polpo/open-retro-storage-frontpanel/sw-frontpanel/main/web_server.cpp

// SPDX-License-Identifier: GPL-2.0-only
//
//  Copyright (C) 2025  Ian Scott
//
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
#include "web_server.h"
#include <string.h>
#include <stdlib.h>
#include <ctype.h>
#include <inttypes.h>
#include <sys/param.h>  // MIN()
#include "esp_log.h"
#include "esp_http_server.h"
#include "esp_system.h"
#include "esp_app_desc.h"
#include "cJSON.h"
#include "interface_common.h"
#include "json_stream.h"
#include "ota_manager.h"
#include "wifi_manager.h"
#ifdef CONFIG_PANEL_TEST_HOOKS
#include <strings.h>
#include "freertos/FreeRTOS.h"
#include "freertos/task.h"
#include "gpio_handler.h"
#include "test_hooks.h"
#endif

static const char *TAG = "web_server";

// Forward declarations
static esp_err_t static_file_handler(httpd_req_t *req);
static esp_err_t api_status_handler(httpd_req_t *req);
static esp_err_t api_images_handler(httpd_req_t *req);
static esp_err_t api_select_entry_handler(httpd_req_t *req);
static esp_err_t api_eject_image_handler(httpd_req_t *req);
static esp_err_t api_prev_image_handler(httpd_req_t *req);
static esp_err_t api_next_image_handler(httpd_req_t *req);
static esp_err_t api_wifi_scan_handler(httpd_req_t *req);
static esp_err_t api_wifi_connect_handler(httpd_req_t *req);
static esp_err_t api_wifi_status_handler(httpd_req_t *req);
static esp_err_t api_settings_get_handler(httpd_req_t *req);
static esp_err_t api_settings_set_handler(httpd_req_t *req);
static esp_err_t api_firmware_check_handler(httpd_req_t *req);
static esp_err_t api_firmware_update_handler(httpd_req_t *req);
static esp_err_t api_firmware_status_handler(httpd_req_t *req);
#ifdef CONFIG_PRODUCT_BLUESCSI
static esp_err_t api_initiator_handler(httpd_req_t *req);
static esp_err_t api_mainboard_firmware_check_handler(httpd_req_t *req);
static esp_err_t api_mainboard_firmware_update_handler(httpd_req_t *req);
static esp_err_t api_mainboard_firmware_status_handler(httpd_req_t *req);
static esp_err_t api_mainboard_firmware_upload_handler(httpd_req_t *req);
static esp_err_t api_panel_firmware_upload_handler(httpd_req_t *req);
static esp_err_t api_delete_handler(httpd_req_t *req);
static esp_err_t api_rename_handler(httpd_req_t *req);
static esp_err_t api_touch_handler(httpd_req_t *req);
static esp_err_t api_mkdir_handler(httpd_req_t *req);
#endif
static esp_err_t api_devices_handler(httpd_req_t *req);
static esp_err_t api_upload_handler(httpd_req_t *req);
static esp_err_t api_download_handler(httpd_req_t *req);
#ifdef CONFIG_PANEL_TEST_HOOKS
static esp_err_t api_button_handler(httpd_req_t *req);
static esp_err_t api_ui_handler(httpd_req_t *req);
static esp_err_t api_screen_handler(httpd_req_t *req);
#endif

// Global server instance for handlers
static web_server_t *g_server = NULL;

// Helper: extract device index from the JSON body. Every request that operates on
// a device should include it in the body, so if there is not one, return false.
static bool get_device_from_body(httpd_req_t *req, uint16_t *device_index) {
    if (req->content_len == 0 || req->content_len > 256) return false;
    char buf[256];
    int len = httpd_req_recv(req, buf, sizeof(buf) - 1);
    if (len <= 0) return false;
    buf[len] = '\0';
    cJSON *json = cJSON_Parse(buf);
    if (!json) return false;
    cJSON *dev = cJSON_GetObjectItem(json, "device");
    bool found = cJSON_IsNumber(dev);
    if (found) *device_index = (uint16_t)dev->valueint;
    cJSON_Delete(json);
    return found;
}

#ifdef CONFIG_PANEL_TEST_HOOKS
// Button ids as wired in main.c: 0=UP 1=SELECT 2=DOWN 3=BACK.
static int button_id_from_name(const char *name) {
    if (!name) return -1;
    if (!strcasecmp(name, "up"))     return 0;
    if (!strcasecmp(name, "select")) return 1;
    if (!strcasecmp(name, "down"))   return 2;
    if (!strcasecmp(name, "back"))   return 3;
    return -1;
}

// POST /api/button  {"button":"down","type":"click","count":1}
// Only click and repeat exist as far as the UI is concerned; the other event
// types the driver emits are never matched by handle_button_event().
static esp_err_t api_button_handler(httpd_req_t *req) {
    char buf[192];
    if (req->content_len == 0 || req->content_len >= sizeof(buf)) {
        httpd_resp_send_err(req, HTTPD_400_BAD_REQUEST, "body required");
        return ESP_FAIL;
    }
    int len = httpd_req_recv(req, buf, sizeof(buf) - 1);
    if (len <= 0) {
        httpd_resp_send_err(req, HTTPD_400_BAD_REQUEST, "short read");
        return ESP_FAIL;
    }
    buf[len] = '\0';

    cJSON *json = cJSON_Parse(buf);
    if (!json) {
        httpd_resp_send_err(req, HTTPD_400_BAD_REQUEST, "bad json");
        return ESP_FAIL;
    }

    cJSON *jb = cJSON_GetObjectItem(json, "button");
    int id = cJSON_IsString(jb) ? button_id_from_name(jb->valuestring)
           : (cJSON_IsNumber(jb) ? jb->valueint : -1);

    cJSON *jt = cJSON_GetObjectItem(json, "type");
    button_event_type_t type = BUTTON_EVENT_CLICK;
    if (cJSON_IsString(jt) && !strcasecmp(jt->valuestring, "repeat")) {
        type = BUTTON_EVENT_REPEAT;
    }

    cJSON *jc = cJSON_GetObjectItem(json, "count");
    int count = cJSON_IsNumber(jc) ? jc->valueint : 1;
    cJSON_Delete(json);

    if (id < 0 || id > 3) {
        httpd_resp_send_err(req, HTTPD_400_BAD_REQUEST, "button must be up|select|down|back");
        return ESP_FAIL;
    }
    if (count < 1 || count > 32) {
        httpd_resp_send_err(req, HTTPD_400_BAD_REQUEST, "count must be 1..32");
        return ESP_FAIL;
    }

    int sent = 0;
    esp_err_t err = ESP_OK;
    for (int i = 0; i < count; i++) {
        err = gpio_handler_inject_event((uint8_t)id, type);
        if (err != ESP_OK) break;
        sent++;
        // Let gpio_event_task drain and the UI settle between presses, so a
        // burst behaves like a person pressing rather than a queue dump.
        vTaskDelay(pdMS_TO_TICKS(30));
    }

    httpd_resp_set_type(req, "application/json");
    JsonStreamWriter jw(req);
    jw.beginObject();
    jw.write("success", err == ESP_OK);
    jw.write("sent", (int)sent);
    if (err != ESP_OK) jw.write("error", esp_err_to_name(err));
    jw.endObject();
    return jw.finalize();
}

// GET /api/ui - what the panel is showing right now.
static esp_err_t api_ui_handler(httpd_req_t *req) {
    panel_ui_state_t st;
    panel_get_ui_state(&st);

    httpd_resp_set_type(req, "application/json");
    JsonStreamWriter jw(req);
    jw.beginObject();
    jw.write("screen", st.screen_name);
    jw.write("screen_id", (int)st.screen);
    jw.write("has_menu", st.has_menu);
    jw.write("cursor", (uint32_t)st.cursor);
    jw.write("count", (uint32_t)st.count);
    jw.write("entry_index", (int)st.entry_index);
    jw.write("selected", st.selected);
    jw.write("display_state", st.display_state_name ? st.display_state_name : "UNKNOWN");
    jw.endObject();
    return jw.finalize();
}

// GET /api/screen - raw u8g2 tile buffer. Geometry rides in headers so the host
// converter does not hardcode the panel or its rotation.
static esp_err_t api_screen_handler(httpd_req_t *req) {
    int tw = 0, th = 0, rot = -1;
    uint8_t *buf = (uint8_t *)malloc(PANEL_FB_MAX_BYTES);
    if (!buf) {
        httpd_resp_send_err(req, HTTPD_500_INTERNAL_SERVER_ERROR, "oom");
        return ESP_FAIL;
    }
    size_t len = panel_get_framebuffer(buf, PANEL_FB_MAX_BYTES, &tw, &th, &rot);
    if (len == 0) {
        free(buf);
        httpd_resp_send_err(req, HTTPD_500_INTERNAL_SERVER_ERROR, "no framebuffer");
        return ESP_FAIL;
    }
    char v[16];
    snprintf(v, sizeof(v), "%d", tw);  httpd_resp_set_hdr(req, "X-Panel-Tile-Width", v);
    char v2[16];
    snprintf(v2, sizeof(v2), "%d", th); httpd_resp_set_hdr(req, "X-Panel-Tile-Height", v2);
    char v3[16];
    snprintf(v3, sizeof(v3), "%d", rot); httpd_resp_set_hdr(req, "X-Panel-Rotation", v3);
    httpd_resp_set_type(req, "application/octet-stream");
    esp_err_t ret = httpd_resp_send(req, (const char *)buf, len);
    free(buf);
    return ret;
}
#endif // CONFIG_PANEL_TEST_HOOKS

// Global OTA manager instance
static ota_manager_t g_ota_manager;

#ifdef CONFIG_PRODUCT_BLUESCSI
static TaskHandle_t g_ota_task_handle = NULL;

// Background OTA task - processes OTA update without blocking HTTP handler
static void web_firmware_update_task(void *pvParameters) {
    ota_manager_t *ota = (ota_manager_t *)pvParameters;

    while (1) {
        esp_err_t ret = ota_manager_process(ota);
        if (ret != ESP_OK && ret != ESP_ERR_NOT_FINISHED) {
            ESP_LOGE(TAG, "OTA process error: %s", esp_err_to_name(ret));
            break;
        }

        ota_state_t state = ota_manager_get_state(ota);

        if (state == OTA_STATE_SUCCESS) {
            ESP_LOGI(TAG, "Web OTA update successful, restarting in 3 seconds...");
            vTaskDelay(pdMS_TO_TICKS(3000));
            esp_restart();
        } else if (state == OTA_STATE_ERROR) {
            ESP_LOGE(TAG, "Web OTA update failed");
            break;
        }

        taskYIELD();
    }

    g_ota_task_handle = NULL;
    vTaskDelete(NULL);
}
#endif

// Embedded file content (gzipped, symbols created by CMakeLists.txt)
extern const uint8_t index_html_gz_start[] asm("_binary_index_html_gz_start");
extern const uint8_t index_html_gz_end[] asm("_binary_index_html_gz_end");
extern const uint8_t app_js_gz_start[] asm("_binary_app_js_gz_start");
extern const uint8_t app_js_gz_end[] asm("_binary_app_js_gz_end");
extern const uint8_t sha256_js_gz_start[] asm("_binary_sha256_js_gz_start");
extern const uint8_t sha256_js_gz_end[] asm("_binary_sha256_js_gz_end");
extern const uint8_t logo_svg_gz_start[] asm("_binary_logo_svg_gz_start");
extern const uint8_t logo_svg_gz_end[] asm("_binary_logo_svg_gz_end");

// Static file descriptor for common handler
typedef struct {
    const uint8_t *start;
    const uint8_t *end;
    const char *content_type;
} static_file_t;

static const static_file_t file_index_html = {
    index_html_gz_start, index_html_gz_end, "text/html; charset=utf-8"
};
static const static_file_t file_app_js = {
    app_js_gz_start, app_js_gz_end, "application/javascript; charset=utf-8"
};
static const static_file_t file_sha256_js = {
    sha256_js_gz_start, sha256_js_gz_end, "application/javascript; charset=utf-8"
};
static const static_file_t file_logo_svg = {
    logo_svg_gz_start, logo_svg_gz_end, "image/svg+xml"
};

// URI handlers
static const httpd_uri_t uri_handlers[] = {
    { .uri = "/", .method = HTTP_GET, .handler = static_file_handler, .user_ctx = (void *)&file_index_html },
    { .uri = "/app.js", .method = HTTP_GET, .handler = static_file_handler, .user_ctx = (void *)&file_app_js },
    { .uri = "/sha256.js", .method = HTTP_GET, .handler = static_file_handler, .user_ctx = (void *)&file_sha256_js },
    { .uri = "/logo.svg", .method = HTTP_GET, .handler = static_file_handler, .user_ctx = (void *)&file_logo_svg },
    { .uri = "/api/status", .method = HTTP_GET, .handler = api_status_handler, .user_ctx = NULL },
    { .uri = "/api/devices", .method = HTTP_GET, .handler = api_devices_handler, .user_ctx = NULL },
    { .uri = "/api/images", .method = HTTP_GET, .handler = api_images_handler, .user_ctx = NULL },
    { .uri = "/api/select_entry", .method = HTTP_POST, .handler = api_select_entry_handler, .user_ctx = NULL },
    { .uri = "/api/eject_image", .method = HTTP_POST, .handler = api_eject_image_handler, .user_ctx = NULL },
    { .uri = "/api/prev_image", .method = HTTP_POST, .handler = api_prev_image_handler, .user_ctx = NULL },
    { .uri = "/api/next_image", .method = HTTP_POST, .handler = api_next_image_handler, .user_ctx = NULL },
    { .uri = "/api/wifi/scan", .method = HTTP_GET, .handler = api_wifi_scan_handler, .user_ctx = NULL },
    { .uri = "/api/wifi/connect", .method = HTTP_POST, .handler = api_wifi_connect_handler, .user_ctx = NULL },
    { .uri = "/api/wifi/status", .method = HTTP_GET, .handler = api_wifi_status_handler, .user_ctx = NULL },
    { .uri = "/api/settings", .method = HTTP_GET, .handler = api_settings_get_handler, .user_ctx = NULL },
    { .uri = "/api/settings", .method = HTTP_POST, .handler = api_settings_set_handler, .user_ctx = NULL },
    { .uri = "/api/firmware/check", .method = HTTP_GET, .handler = api_firmware_check_handler, .user_ctx = NULL },
    { .uri = "/api/firmware/update", .method = HTTP_POST, .handler = api_firmware_update_handler, .user_ctx = NULL },
    { .uri = "/api/firmware/status", .method = HTTP_GET, .handler = api_firmware_status_handler, .user_ctx = NULL },
#ifdef CONFIG_PRODUCT_BLUESCSI
    { .uri = "/api/initiator", .method = HTTP_GET, .handler = api_initiator_handler, .user_ctx = NULL },
    { .uri = "/api/firmware/mainboard/check", .method = HTTP_GET, .handler = api_mainboard_firmware_check_handler, .user_ctx = NULL },
    { .uri = "/api/firmware/mainboard/update", .method = HTTP_POST, .handler = api_mainboard_firmware_update_handler, .user_ctx = NULL },
    { .uri = "/api/firmware/mainboard/status", .method = HTTP_GET, .handler = api_mainboard_firmware_status_handler, .user_ctx = NULL },
    { .uri = "/api/firmware/mainboard/upload", .method = HTTP_POST, .handler = api_mainboard_firmware_upload_handler, .user_ctx = NULL },
    { .uri = "/api/firmware/panel/upload", .method = HTTP_POST, .handler = api_panel_firmware_upload_handler, .user_ctx = NULL },
    { .uri = "/api/delete", .method = HTTP_POST, .handler = api_delete_handler, .user_ctx = NULL },
    { .uri = "/api/rename", .method = HTTP_POST, .handler = api_rename_handler, .user_ctx = NULL },
    { .uri = "/api/touch", .method = HTTP_POST, .handler = api_touch_handler, .user_ctx = NULL },
    { .uri = "/api/mkdir", .method = HTTP_POST, .handler = api_mkdir_handler, .user_ctx = NULL },
#endif
    { .uri = "/api/upload", .method = HTTP_POST, .handler = api_upload_handler, .user_ctx = NULL },
    { .uri = "/api/download", .method = HTTP_GET, .handler = api_download_handler, .user_ctx = NULL },
#ifdef CONFIG_PANEL_TEST_HOOKS
    { .uri = "/api/button", .method = HTTP_POST, .handler = api_button_handler, .user_ctx = NULL },
    { .uri = "/api/ui", .method = HTTP_GET, .handler = api_ui_handler, .user_ctx = NULL },
    { .uri = "/api/screen", .method = HTTP_GET, .handler = api_screen_handler, .user_ctx = NULL }
#endif
};

// ETag for the embedded web assets, based on the build's ELF hash
static char s_asset_etag[CONFIG_APP_RETRIEVE_LEN_ELF_SHA + 3];

static void asset_etag_init(void) {
    char sha[CONFIG_APP_RETRIEVE_LEN_ELF_SHA + 1] = {0};
    esp_app_get_elf_sha256(sha, sizeof(sha));
    // ETags must be double-quoted per RFC 9110
    snprintf(s_asset_etag, sizeof(s_asset_etag), "\"%s\"", sha);
}

static esp_err_t static_file_handler(httpd_req_t *req) {
    const static_file_t *file = (const static_file_t *)req->user_ctx;

    httpd_resp_set_type(req, file->content_type);
    httpd_resp_set_hdr(req, "Cache-Control", "no-cache");
    httpd_resp_set_hdr(req, "ETag", s_asset_etag);

    char if_none_match[sizeof(s_asset_etag)];
    if (httpd_req_get_hdr_value_str(req, "If-None-Match", if_none_match, sizeof(if_none_match)) == ESP_OK &&
        strcmp(if_none_match, s_asset_etag) == 0) {
        httpd_resp_set_status(req, "304 Not Modified");
        return httpd_resp_send(req, NULL, 0);
    }

    httpd_resp_set_hdr(req, "Content-Encoding", "gzip");
    return httpd_resp_send(req, (const char *)file->start, file->end - file->start);
}

static esp_err_t api_status_handler(httpd_req_t *req) {
    httpd_resp_set_type(req, "application/json");

    JsonStreamWriter json(req);
    esp_err_t ret = json.beginObject();
    if (ret != ESP_OK) return ret;

    if (g_server && g_server->interface_ctx) {
        system_info_t sys_info;
        esp_err_t info_ret = interface_get_system_info(g_server->interface_ctx, &sys_info);
        if (info_ret == ESP_OK) {
            ret = json.write("main_firmware", sys_info.main_firmware_version);
            if (ret != ESP_OK) return ret;
            ret = json.write("panel_firmware", sys_info.panel_firmware_version);
            if (ret != ESP_OK) return ret;
            ret = json.write("transport", sys_info.transport_name);
            if (ret != ESP_OK) return ret;
            ret = json.write("host_connected", sys_info.host_connected ? 1 : 0);
            if (ret != ESP_OK) return ret;
            ret = json.write("free_memory", sys_info.free_memory);
            if (ret != ESP_OK) return ret;
            ret = json.write("uptime", sys_info.uptime_seconds);
            if (ret != ESP_OK) return ret;
        } else {
            ret = json.write("main_firmware", "");
            if (ret != ESP_OK) return ret;
            ret = json.write("panel_firmware", "");
            if (ret != ESP_OK) return ret;
            ret = json.write("transport", "None");
            if (ret != ESP_OK) return ret;
            ret = json.write("host_connected", 0);
            if (ret != ESP_OK) return ret;
            ret = json.write("free_memory", (uint32_t)esp_get_free_heap_size());
            if (ret != ESP_OK) return ret;
            ret = json.write("uptime", (uint32_t)(esp_log_timestamp() / 1000));
            if (ret != ESP_OK) return ret;
        }
    } else {
        ret = json.write("main_firmware", "");
        if (ret != ESP_OK) return ret;
        ret = json.write("panel_firmware", "");
        if (ret != ESP_OK) return ret;
        ret = json.write("transport", "None");
        if (ret != ESP_OK) return ret;
        ret = json.write("host_connected", 0);
        if (ret != ESP_OK) return ret;
        ret = json.write("free_memory", (uint32_t)esp_get_free_heap_size());
        if (ret != ESP_OK) return ret;
        ret = json.write("uptime", (uint32_t)(esp_log_timestamp() / 1000));
        if (ret != ESP_OK) return ret;
    }

    ret = json.write("product_name", PRODUCT_NAME_SHORT);
    if (ret != ESP_OK) return ret;
    ret = json.write("product_full", PRODUCT_NAME_FULL);
    if (ret != ESP_OK) return ret;
    ret = json.write("hostname", (g_server && g_server->interface_ctx)
                                     ? wifi_manager_get_mdns_hostname(g_server->interface_ctx->wifi_manager)
                                     : WIFI_MANAGER_MDNS_HOSTNAME_DEFAULT);
    if (ret != ESP_OK) return ret;
    ret = json.write("logo_url", PRODUCT_LOGO_URL);
    if (ret != ESP_OK) return ret;

    ret = json.endObject();
    if (ret != ESP_OK) return ret;

    return json.finalize();
}

#ifdef CONFIG_PRODUCT_BLUESCSI
static const char *initiator_phase_name(uint8_t phase) {
    switch (phase) {
        case PANEL_INITIATOR_PHASE_SCANNING: return "scanning";
        case PANEL_INITIATOR_PHASE_IMAGING:  return "imaging";
        case PANEL_INITIATOR_PHASE_COMPLETE: return "complete";
        case PANEL_INITIATOR_PHASE_ERROR:    return "error";
        default:                             return "idle";
    }
}

/* Serves the status the display task already polls. Issuing our own transaction
 * here would put a browser refresh in contention with the display task for the
 * host_comm mutex, against a main board that may be mid-spin-up. */
static esp_err_t api_initiator_handler(httpd_req_t *req) {
    httpd_resp_set_type(req, "application/json");

    JsonStreamWriter json(req);
    esp_err_t ret = json.beginObject();
    if (ret != ESP_OK) return ret;

    int target_count = 0;
    const initiator_status_response_t *st = panel_get_initiator_status(&target_count);

    ret = json.write("mode", panel_in_initiator_mode() ? 1 : 0);
    if (ret != ESP_OK) return ret;

    if (!st || !panel_in_initiator_mode()) {
        ret = json.endObject();
        if (ret != ESP_OK) return ret;
        return json.finalize();
    }

    // Progress comes from the synchronous summary, which is current even while
    // the board is imaging. The per-target list below comes from the async
    // status and may be older.
    const panel_initiator_summary_t *sum = panel_get_initiator_summary();

    ret = json.write("phase", (int)sum->phase);
    if (ret != ESP_OK) return ret;
    ret = json.write("phase_name", initiator_phase_name(sum->phase));
    if (ret != ESP_OK) return ret;
    ret = json.write("progress", (int)sum->progress);
    if (ret != ESP_OK) return ret;
    ret = json.write("initiator_id", (int)st->initiator_id);
    if (ret != ESP_OK) return ret;
    ret = json.write("current_target", (int)sum->current_target);
    if (ret != ESP_OK) return ret;
    ret = json.write("targets_found", (int)sum->targets_found);
    if (ret != ESP_OK) return ret;
    ret = json.write("targets_imaged", (int)sum->targets_imaged);
    if (ret != ESP_OK) return ret;
    // Identity of the target in progress, so the page can say what it is
    // working on rather than just how fast. From the summary, because the
    // per-target table below does not arrive while the board is imaging.
    ret = json.write("device_type", (int)sum->device_type);
    if (ret != ESP_OK) return ret;
    ret = json.write("vendor", sum->vendor);
    if (ret != ESP_OK) return ret;
    ret = json.write("product", sum->product);
    if (ret != ESP_OK) return ret;
    ret = json.write("size_kb",
                     (uint32_t)((uint64_t)sum->sectorcount * sum->sectorsize / 1024));
    if (ret != ESP_OK) return ret;
    ret = json.write("speed_kbps", (uint32_t)sum->speed_kbps);
    if (ret != ESP_OK) return ret;
    ret = json.write("filename", st->current_filename);
    if (ret != ESP_OK) return ret;

    ret = json.writeKey("targets");
    if (ret != ESP_OK) return ret;
    ret = json.beginArray();
    if (ret != ESP_OK) return ret;

    for (int i = 0; i < target_count; i++) {
        const initiator_target_info_t *t = &st->targets[i];
        char vendor[9], product[17];
        memcpy(vendor, t->vendor, 8);   vendor[8] = '\0';
        memcpy(product, t->product, 16); product[16] = '\0';
        for (int j = 7; j >= 0 && vendor[j] == ' '; j--) vendor[j] = '\0';
        for (int j = 15; j >= 0 && product[j] == ' '; j--) product[j] = '\0';

        ret = json.beginObject();
        if (ret != ESP_OK) return ret;
        ret = json.write("id", (int)t->scsi_id);
        if (ret != ESP_OK) return ret;
        ret = json.write("type", (int)t->device_type);
        if (ret != ESP_OK) return ret;
        ret = json.write("status", (int)t->status);
        if (ret != ESP_OK) return ret;
        ret = json.write("skip_reason", (int)t->skip_reason);
        if (ret != ESP_OK) return ret;
        ret = json.write("vendor", vendor);
        if (ret != ESP_OK) return ret;
        ret = json.write("product", product);
        if (ret != ESP_OK) return ret;
        ret = json.write("sectors", t->sectorcount);
        if (ret != ESP_OK) return ret;
        ret = json.write("sector_size", t->sectorsize);
        if (ret != ESP_OK) return ret;
        ret = json.write("sectors_done", t->sectors_done);
        if (ret != ESP_OK) return ret;
        ret = json.write("bad_sectors", t->bad_sector_count);
        if (ret != ESP_OK) return ret;
        ret = json.endObject();
        if (ret != ESP_OK) return ret;
    }

    ret = json.endArray();
    if (ret != ESP_OK) return ret;
    ret = json.endObject();
    if (ret != ESP_OK) return ret;
    return json.finalize();
}
#endif // CONFIG_PRODUCT_BLUESCSI

static esp_err_t api_devices_handler(httpd_req_t *req) {
    httpd_resp_set_type(req, "application/json");

    JsonStreamWriter json(req);
    esp_err_t ret = json.beginObject();
    if (ret != ESP_OK) return ret;

    if (g_server && g_server->interface_ctx) {
        uint16_t active_device = g_server->interface_ctx->active_device_index;
        ret = json.write("active_device", (int)active_device);
        if (ret != ESP_OK) return ret;

        // Get device list from host
        uint8_t buf[sizeof(device_list_response_t) + CONFIG_MAX_DEVICES * sizeof(device_summary_t)];
        device_list_response_t *list = (device_list_response_t *)buf;

        esp_err_t list_ret = interface_get_device_list(g_server->interface_ctx, list, sizeof(buf));

        if (list_ret == ESP_OK) {
            ret = json.write("device_count", (int)list->device_count);
            if (ret != ESP_OK) return ret;
#ifdef CONFIG_PRODUCT_BLUESCSI
            // In initiator mode there are no emulated devices; the web UI needs
            // to know that rather than reading the empty list as a failure.
            ret = json.write("mode", (int)PANEL_DEVLIST_MODE(list));
            if (ret != ESP_OK) return ret;
#endif

            ret = json.writeKey("devices");
            if (ret != ESP_OK) return ret;
            ret = json.beginArray();
            if (ret != ESP_OK) return ret;

            for (uint8_t i = 0; i < list->device_count; i++) {
                ret = json.beginObject();
                if (ret != ESP_OK) return ret;

                ret = json.write("index", (int)list->devices[i].device_index);
                if (ret != ESP_OK) return ret;
                ret = json.write("type", (int)list->devices[i].device_type);
                if (ret != ESP_OK) return ret;
                ret = json.write("status", (int)list->devices[i].device_status);
                if (ret != ESP_OK) return ret;
                ret = json.write("label", list->devices[i].device_label);
                if (ret != ESP_OK) return ret;
                ret = json.write("image", list->devices[i].image_name);
                if (ret != ESP_OK) return ret;

                ret = json.endObject();
                if (ret != ESP_OK) return ret;
            }

            ret = json.endArray();
            if (ret != ESP_OK) return ret;
        } else {
            ret = json.write("device_count", 0);
            if (ret != ESP_OK) return ret;
            ret = json.writeKey("devices");
            if (ret != ESP_OK) return ret;
            ret = json.beginArray();
            if (ret != ESP_OK) return ret;
            ret = json.endArray();
            if (ret != ESP_OK) return ret;
            ret = json.write("error", esp_err_to_name(list_ret));
            if (ret != ESP_OK) return ret;
        }
    } else {
        ret = json.write("active_device", 0);
        if (ret != ESP_OK) return ret;
        ret = json.write("device_count", 0);
        if (ret != ESP_OK) return ret;
        ret = json.writeKey("devices");
        if (ret != ESP_OK) return ret;
        ret = json.beginArray();
        if (ret != ESP_OK) return ret;
        ret = json.endArray();
        if (ret != ESP_OK) return ret;
    }

    ret = json.endObject();
    if (ret != ESP_OK) return ret;

    return json.finalize();
}

static esp_err_t api_images_handler(httpd_req_t *req) {
    httpd_resp_set_type(req, "application/json");

    // The ?device= query parameter names the device this listing is for.
    // On BlueSCSI: used for the device's loaded image status
    // On PicoIDE: loaded image status, per-device browse dir, extension filter
    //
    // Unlike the commands that act on a device, a listing is a read and can fall
    // back to the panel's own selection — the same value /api/devices reports as
    // active_device. A client that has no device list yet (BlueSCSI reports none
    // while imaging in initiator mode) can still browse the card, and adopts the
    // echoed index for its next request.
    uint16_t device_index = (g_server && g_server->interface_ctx)
        ? g_server->interface_ctx->active_device_index : 0;
    {
        char query[64];
        char device_str[8];
        if (httpd_req_get_url_query_len(req) > 0 &&
            httpd_req_get_url_query_str(req, query, sizeof(query)) == ESP_OK &&
            httpd_query_key_value(query, "device", device_str, sizeof(device_str)) == ESP_OK) {
            device_index = (uint16_t)atoi(device_str);
        }
    }

    JsonStreamWriter json(req);
    esp_err_t ret = json.beginObject();
    if (ret != ESP_OK) return ret;

    if (g_server && g_server->interface_ctx) {
        host_comm_t *host_comm = g_server->interface_ctx->host_comm;

        ret = json.write("device", (int)device_index);
        if (ret != ESP_OK) return ret;

        // Get current path
        char current_path[256] = "/";
        if (host_comm && host_comm->link_up) {
            host_comm_get_current_path(host_comm, device_index, current_path, sizeof(current_path));
        }
        ret = json.write("current_path", current_path);
        if (ret != ESP_OK) return ret;

        // Get loaded image status
        loaded_image_status_t image_status = {};
        bool have_image_status = false;
        if (host_comm && host_comm->link_up) {
            have_image_status = (host_comm_get_loaded_image_status(host_comm, device_index, &image_status) == ESP_OK);
        }

        if (have_image_status && image_status.image_loaded) {
            ret = json.write("current_image", image_status.image_name);
            if (ret != ESP_OK) return ret;
            ret = json.write("image_index", image_status.image_index);
            if (ret != ESP_OK) return ret;
            ret = json.write("total_images", image_status.total_images);
            if (ret != ESP_OK) return ret;
        } else {
            ret = json.write("current_image", (const char*)nullptr);
            if (ret != ESP_OK) return ret;
            ret = json.write("image_index", 0);
            if (ret != ESP_OK) return ret;
            ret = json.write("total_images", 0);
            if (ret != ESP_OK) return ret;
        }

        // Start entries array
        ret = json.writeKey("entries");
        if (ret != ESP_OK) return ret;

        ret = json.beginArray();
        if (ret != ESP_OK) return ret;

        // Stream entries one at a time to avoid stack overflow
        uint32_t entry_count = 0;
        if (host_comm && host_comm->link_up) {
            host_comm_get_entry_count(host_comm, device_index, &entry_count);
        }

        for (uint32_t i = 0; i < entry_count && i < 64; i++) {
            dir_entry_info_t entry;
            if (host_comm_get_entry_info(host_comm, device_index, i, &entry) == ESP_OK) {
                ret = json.beginObject();
                if (ret != ESP_OK) return ret;

                ret = json.write("name", entry.name);
                if (ret != ESP_OK) return ret;

                ret = json.write("is_directory", entry.entry_type == 0);
                if (ret != ESP_OK) return ret;
                // log.txt / bluescsi.ini and friends stay listed so they can be
                // downloaded and edited, but must not offer a Load button.
                ret = json.write("loadable",
                                 (entry.flags & PANEL_ENTRY_FLAG_NOT_LOADABLE) ? 0 : 1);
                if (ret != ESP_OK) return ret;

                ret = json.write("index", (int)i);
                if (ret != ESP_OK) return ret;

                ret = json.endObject();
                if (ret != ESP_OK) return ret;
            }
        }

        ret = json.endArray();
        if (ret != ESP_OK) return ret;
    } else {
        ret = json.write("current_path", "/");
        if (ret != ESP_OK) return ret;

        ret = json.write("current_image", (const char*)nullptr);
        if (ret != ESP_OK) return ret;

        ret = json.write("image_index", 0);
        if (ret != ESP_OK) return ret;

        ret = json.write("total_images", 0);
        if (ret != ESP_OK) return ret;

        ret = json.writeKey("entries");
        if (ret != ESP_OK) return ret;

        ret = json.beginArray();
        if (ret != ESP_OK) return ret;

        ret = json.endArray();
        if (ret != ESP_OK) return ret;
    }

    ret = json.endObject();
    if (ret != ESP_OK) return ret;

    return json.finalize();
}

static esp_err_t api_select_entry_handler(httpd_req_t *req) {
    // Read request body
    char content[100];
    size_t recv_size = MIN(req->content_len, sizeof(content) - 1);
    int ret = httpd_req_recv(req, content, recv_size);
    if (ret <= 0) {
        httpd_resp_send_500(req);
        return ESP_FAIL;
    }
    content[ret] = '\0';

    // Parse JSON
    cJSON *json = cJSON_Parse(content);
    if (!json) {
        httpd_resp_send_err(req, HTTPD_400_BAD_REQUEST, "Invalid JSON");
        return ESP_FAIL;
    }

    cJSON *entry_index_json = cJSON_GetObjectItem(json, "index");
    if (!cJSON_IsNumber(entry_index_json)) {
        cJSON_Delete(json);
        httpd_resp_send_err(req, HTTPD_400_BAD_REQUEST, "Missing or invalid index");
        return ESP_FAIL;
    }

    int32_t entry_index = (int32_t)entry_index_json->valueint;

    // The device to act on is required
    cJSON *device_json = cJSON_GetObjectItem(json, "device");
    if (!cJSON_IsNumber(device_json)) {
        cJSON_Delete(json);
        httpd_resp_send_err(req, HTTPD_400_BAD_REQUEST, "Missing device");
        return ESP_FAIL;
    }
    uint16_t device_index = (uint16_t)device_json->valueint;

    // Send command to host
    httpd_resp_set_type(req, "application/json");

    JsonStreamWriter json_writer(req);
    esp_err_t json_ret = json_writer.beginObject();
    if (json_ret != ESP_OK) {
        cJSON_Delete(json);
        return json_ret;
    }

    bool success = false;
    if (g_server && g_server->interface_ctx) {
        esp_err_t select_ret = interface_select_entry(g_server->interface_ctx, entry_index, device_index);
        success = (select_ret == ESP_OK);
        interface_invalidate_disc_list();
        if (!success) {
            json_ret = json_writer.write("error", esp_err_to_name(select_ret));
            if (json_ret != ESP_OK) {
                cJSON_Delete(json);
                return json_ret;
            }
        }
    } else {
        json_ret = json_writer.write("error", "Interface not available");
        if (json_ret != ESP_OK) {
            cJSON_Delete(json);
            return json_ret;
        }
    }

    json_ret = json_writer.write("success", success);
    if (json_ret != ESP_OK) {
        cJSON_Delete(json);
        return json_ret;
    }

    json_ret = json_writer.endObject();
    if (json_ret != ESP_OK) {
        cJSON_Delete(json);
        return json_ret;
    }

    cJSON_Delete(json);
    return json_writer.finalize();
}

static esp_err_t api_eject_image_handler(httpd_req_t *req) {
    uint16_t device_index;
    if (!get_device_from_body(req, &device_index)) {
        httpd_resp_send_err(req, HTTPD_400_BAD_REQUEST, "Missing device");
        return ESP_FAIL;
    }

    httpd_resp_set_type(req, "application/json");

    JsonStreamWriter json(req);
    esp_err_t ret = json.beginObject();
    if (ret != ESP_OK) return ret;

    bool success = false;
    if (g_server && g_server->interface_ctx) {
        esp_err_t eject_ret = interface_eject_image(g_server->interface_ctx, device_index);
        success = (eject_ret == ESP_OK);
        if (!success) {
            ret = json.write("error", esp_err_to_name(eject_ret));
            if (ret != ESP_OK) return ret;
        }
    } else {
        ret = json.write("error", "Interface not available");
        if (ret != ESP_OK) return ret;
    }

    ret = json.write("success", success);
    if (ret != ESP_OK) return ret;

    ret = json.endObject();
    if (ret != ESP_OK) return ret;

    return json.finalize();
}

static esp_err_t api_prev_image_handler(httpd_req_t *req) {
    uint16_t device_index;
    if (!get_device_from_body(req, &device_index)) {
        httpd_resp_send_err(req, HTTPD_400_BAD_REQUEST, "Missing device");
        return ESP_FAIL;
    }

    httpd_resp_set_type(req, "application/json");

    JsonStreamWriter json(req);
    esp_err_t ret = json.beginObject();
    if (ret != ESP_OK) return ret;

    bool success = false;
    if (g_server && g_server->interface_ctx && g_server->interface_ctx->host_comm) {
        esp_err_t prev_ret = host_comm_select_prev_image(g_server->interface_ctx->host_comm, device_index);
        success = (prev_ret == ESP_OK);
        if (!success) {
            ret = json.write("error", esp_err_to_name(prev_ret));
            if (ret != ESP_OK) return ret;
        }
    } else {
        ret = json.write("error", "Interface not available");
        if (ret != ESP_OK) return ret;
    }

    ret = json.write("success", success);
    if (ret != ESP_OK) return ret;

    ret = json.endObject();
    if (ret != ESP_OK) return ret;

    return json.finalize();
}

static esp_err_t api_next_image_handler(httpd_req_t *req) {
    uint16_t device_index;
    if (!get_device_from_body(req, &device_index)) {
        httpd_resp_send_err(req, HTTPD_400_BAD_REQUEST, "Missing device");
        return ESP_FAIL;
    }

    httpd_resp_set_type(req, "application/json");

    JsonStreamWriter json(req);
    esp_err_t ret = json.beginObject();
    if (ret != ESP_OK) return ret;

    bool success = false;
    if (g_server && g_server->interface_ctx && g_server->interface_ctx->host_comm) {
        esp_err_t next_ret = host_comm_select_next_image(g_server->interface_ctx->host_comm, device_index);
        success = (next_ret == ESP_OK);
        if (!success) {
            ret = json.write("error", esp_err_to_name(next_ret));
            if (ret != ESP_OK) return ret;
        }
    } else {
        ret = json.write("error", "Interface not available");
        if (ret != ESP_OK) return ret;
    }

    ret = json.write("success", success);
    if (ret != ESP_OK) return ret;

    ret = json.endObject();
    if (ret != ESP_OK) return ret;

    return json.finalize();
}

static esp_err_t api_wifi_scan_handler(httpd_req_t *req) {
    httpd_resp_set_type(req, "application/json");

    JsonStreamWriter json(req);
    esp_err_t ret = json.beginObject();
    if (ret != ESP_OK) return ret;

    if (g_server && g_server->interface_ctx && g_server->interface_ctx->wifi_manager) {
        // Start WiFi scan
        esp_err_t scan_ret = wifi_manager_scan_start(g_server->interface_ctx->wifi_manager);

        if (scan_ret != ESP_OK) {
            ret = json.write("error", esp_err_to_name(scan_ret));
            if (ret != ESP_OK) return ret;
        }

        // Get number of APs found
        uint16_t ap_count = 0;
        scan_ret = wifi_manager_scan_get_count(g_server->interface_ctx->wifi_manager, &ap_count);

        if (scan_ret != ESP_OK) {
            ret = json.write("error", esp_err_to_name(scan_ret));
            if (ret != ESP_OK) return ret;
        }

        ret = json.writeKey("networks");
        if (ret != ESP_OK) return ret;

        ret = json.beginArray();
        if (ret != ESP_OK) return ret;

        // Fetch and stream each AP record one at a time
        for (uint16_t i = 0; i < ap_count && i < 32; i++) {
            wifi_ap_info_t ap_info;
            scan_ret = wifi_manager_scan_get_ap(g_server->interface_ctx->wifi_manager, &ap_info);

            if (scan_ret == ESP_OK) {
                ret = json.beginObject();
                if (ret != ESP_OK) {
                    // Clean up remaining APs before returning
                    wifi_manager_scan_cleanup(g_server->interface_ctx->wifi_manager);
                    return ret;
                }

                ret = json.write("ssid", ap_info.ssid);
                if (ret != ESP_OK) {
                    wifi_manager_scan_cleanup(g_server->interface_ctx->wifi_manager);
                    return ret;
                }

                ret = json.write("rssi", ap_info.rssi);
                if (ret != ESP_OK) {
                    wifi_manager_scan_cleanup(g_server->interface_ctx->wifi_manager);
                    return ret;
                }

                ret = json.write("auth_mode", interface_auth_mode_string(ap_info.auth_mode));
                if (ret != ESP_OK) {
                    wifi_manager_scan_cleanup(g_server->interface_ctx->wifi_manager);
                    return ret;
                }

                ret = json.write("has_password", ap_info.has_password ? 1 : 0);
                if (ret != ESP_OK) {
                    wifi_manager_scan_cleanup(g_server->interface_ctx->wifi_manager);
                    return ret;
                }

                ret = json.endObject();
                if (ret != ESP_OK) {
                    wifi_manager_scan_cleanup(g_server->interface_ctx->wifi_manager);
                    return ret;
                }
            }
        }

        // Clean up any remaining AP records (if ap_count > 32)
        wifi_manager_scan_cleanup(g_server->interface_ctx->wifi_manager);

        ret = json.endArray();
        if (ret != ESP_OK) return ret;
    } else {
        // Add mock data when interface is not available
        ret = json.writeKey("networks");
        if (ret != ESP_OK) return ret;

        ret = json.beginArray();
        if (ret != ESP_OK) return ret;

        ret = json.beginObject();
        if (ret != ESP_OK) return ret;

        ret = json.write("ssid", "Example Network");
        if (ret != ESP_OK) return ret;

        ret = json.write("rssi", -45);
        if (ret != ESP_OK) return ret;

        ret = json.write("auth_mode", "WPA2");
        if (ret != ESP_OK) return ret;

        ret = json.write("has_password", 1);
        if (ret != ESP_OK) return ret;

        ret = json.endObject();
        if (ret != ESP_OK) return ret;

        ret = json.endArray();
        if (ret != ESP_OK) return ret;
    }

    ret = json.endObject();
    if (ret != ESP_OK) return ret;

    return json.finalize();
}

static esp_err_t api_wifi_connect_handler(httpd_req_t *req) {
    // Read request body
    char content[256];
    size_t recv_size = MIN(req->content_len, sizeof(content) - 1);
    int ret = httpd_req_recv(req, content, recv_size);
    if (ret <= 0) {
        httpd_resp_send_500(req);
        return ESP_FAIL;
    }
    content[ret] = '\0';

    // Parse JSON
    cJSON *json = cJSON_Parse(content);
    if (!json) {
        httpd_resp_send_err(req, HTTPD_400_BAD_REQUEST, "Invalid JSON");
        return ESP_FAIL;
    }

    cJSON *ssid_json = cJSON_GetObjectItem(json, "ssid");
    cJSON *password_json = cJSON_GetObjectItem(json, "password");

    if (!cJSON_IsString(ssid_json)) {
        cJSON_Delete(json);
        httpd_resp_send_err(req, HTTPD_400_BAD_REQUEST, "Missing or invalid SSID");
        return ESP_FAIL;
    }

    const char *ssid = ssid_json->valuestring;
    const char *password = (cJSON_IsString(password_json)) ? password_json->valuestring : NULL;

    // Connect to WiFi
    httpd_resp_set_type(req, "application/json");

    JsonStreamWriter json_writer(req);
    esp_err_t json_ret = json_writer.beginObject();
    if (json_ret != ESP_OK) {
        cJSON_Delete(json);
        return json_ret;
    }

    bool success = false;
    if (g_server && g_server->interface_ctx) {
        esp_err_t connect_ret = interface_wifi_connect(g_server->interface_ctx, ssid, password);
        success = (connect_ret == ESP_OK);
        if (!success) {
            json_ret = json_writer.write("error", esp_err_to_name(connect_ret));
            if (json_ret != ESP_OK) {
                cJSON_Delete(json);
                return json_ret;
            }
        }
    } else {
        json_ret = json_writer.write("error", "Interface not available");
        if (json_ret != ESP_OK) {
            cJSON_Delete(json);
            return json_ret;
        }
    }

    json_ret = json_writer.write("success", success);
    if (json_ret != ESP_OK) {
        cJSON_Delete(json);
        return json_ret;
    }

    json_ret = json_writer.endObject();
    if (json_ret != ESP_OK) {
        cJSON_Delete(json);
        return json_ret;
    }

    cJSON_Delete(json);
    return json_writer.finalize();
}

static esp_err_t api_wifi_status_handler(httpd_req_t *req) {
    httpd_resp_set_type(req, "application/json");

    JsonStreamWriter json(req);
    esp_err_t ret = json.beginObject();
    if (ret != ESP_OK) return ret;

    if (g_server && g_server->interface_ctx && g_server->interface_ctx->wifi_manager) {
        wifi_manager_t *wifi = g_server->interface_ctx->wifi_manager;
        wifi_manager_state_t state = wifi_manager_get_state(wifi);

        ret = json.write("state", interface_wifi_state_string(state));
        if (ret != ESP_OK) return ret;

        // Determine mode: AP, Client, or None
        const char *mode = "None";
        if (wifi->ap_active) {
            mode = "AP";
        } else if (wifi->station_connected) {
            mode = "Client";
        }
        ret = json.write("mode", mode);
        if (ret != ESP_OK) return ret;

        // Include SSID based on mode
        if (wifi->station_connected) {
            ret = json.write("ssid", wifi->ssid);
            if (ret != ESP_OK) return ret;

            esp_ip4_addr_t ip;
            if (wifi_manager_get_ip_info(wifi, &ip, NULL, NULL) == ESP_OK) {
                char ip_address[16];
                snprintf(ip_address, sizeof(ip_address), IPSTR, IP2STR(&ip));
                ret = json.write("ip_address", ip_address);
                if (ret != ESP_OK) return ret;
            } else {
                ret = json.write("ip_address", "");
                if (ret != ESP_OK) return ret;
            }
        } else if (wifi->ap_active) {
            ret = json.write("ssid", wifi_manager_get_ap_ssid(wifi));
            if (ret != ESP_OK) return ret;

            char ip_address[16];
            snprintf(ip_address, sizeof(ip_address), IPSTR, IP2STR(&wifi->ap_ip_addr));
            ret = json.write("ip_address", ip_address);
            if (ret != ESP_OK) return ret;
        } else {
            ret = json.write("ssid", "");
            if (ret != ESP_OK) return ret;

            ret = json.write("ip_address", "");
            if (ret != ESP_OK) return ret;
        }
    } else {
        ret = json.write("state", "Unavailable");
        if (ret != ESP_OK) return ret;

        ret = json.write("mode", "None");
        if (ret != ESP_OK) return ret;

        ret = json.write("ssid", "");
        if (ret != ESP_OK) return ret;

        ret = json.write("ip_address", "");
        if (ret != ESP_OK) return ret;
    }

    ret = json.endObject();
    if (ret != ESP_OK) return ret;

    return json.finalize();
}

// Panel identity: AP SSID and mDNS hostname
// Defaults are reported so the UI can show them as placeholders
static esp_err_t api_settings_get_handler(httpd_req_t *req) {
    httpd_resp_set_type(req, "application/json");

    JsonStreamWriter json(req);
    esp_err_t ret = json.beginObject();
    if (ret != ESP_OK) return ret;

    char default_ap_ssid[WIFI_MANAGER_SSID_MAX_LEN];
    char default_hostname[WIFI_MANAGER_HOSTNAME_MAX_LEN];
    wifi_manager_default_ap_ssid(default_ap_ssid, sizeof(default_ap_ssid));
    wifi_manager_default_mdns_hostname(default_hostname, sizeof(default_hostname));

    wifi_manager_t *wifi = (g_server && g_server->interface_ctx) ? g_server->interface_ctx->wifi_manager : NULL;

    ret = json.write("ap_ssid", wifi ? wifi_manager_get_ap_ssid(wifi) : default_ap_ssid);
    if (ret != ESP_OK) return ret;
    ret = json.write("mdns_hostname", wifi ? wifi_manager_get_mdns_hostname(wifi) : default_hostname);
    if (ret != ESP_OK) return ret;
    ret = json.write("default_ap_ssid", default_ap_ssid);
    if (ret != ESP_OK) return ret;
    ret = json.write("default_mdns_hostname", default_hostname);
    if (ret != ESP_OK) return ret;

    ret = json.endObject();
    if (ret != ESP_OK) return ret;

    return json.finalize();
}

static esp_err_t api_settings_set_handler(httpd_req_t *req) {
    char content[512];
    size_t recv_size = MIN(req->content_len, sizeof(content) - 1);
    int recv_ret = httpd_req_recv(req, content, recv_size);
    if (recv_ret <= 0) {
        httpd_resp_send_500(req);
        return ESP_FAIL;
    }
    content[recv_ret] = '\0';

    cJSON *json_req = cJSON_Parse(content);
    if (!json_req) {
        httpd_resp_send_err(req, HTTPD_400_BAD_REQUEST, "Invalid JSON");
        return ESP_FAIL;
    }

    wifi_manager_t *wifi = (g_server && g_server->interface_ctx) ? g_server->interface_ctx->wifi_manager : NULL;
    if (!wifi) {
        cJSON_Delete(json_req);
        httpd_resp_send_err(req, HTTPD_500_INTERNAL_SERVER_ERROR, "WiFi manager not available");
        return ESP_FAIL;
    }

    // Any field can be omitted to leave it alone. An empty (but not omitted) field
    // resets it to default
    cJSON *ap_ssid_json = cJSON_GetObjectItem(json_req, "ap_ssid");
    cJSON *ap_password_json = cJSON_GetObjectItem(json_req, "ap_password");
    cJSON *hostname_json = cJSON_GetObjectItem(json_req, "mdns_hostname");
    const char *ap_ssid = cJSON_IsString(ap_ssid_json) ? ap_ssid_json->valuestring : NULL;
    const char *ap_password = cJSON_IsString(ap_password_json) ? ap_password_json->valuestring : NULL;
    const char *hostname = cJSON_IsString(hostname_json) ? hostname_json->valuestring : NULL;

    const char *error = NULL;
    if (ap_ssid && ap_ssid[0] && !wifi_manager_ap_ssid_is_valid(ap_ssid)) {
        error = "Invalid AP name: 1-32 bytes";
    } else if (ap_password && ap_password[0] && !wifi_manager_ap_password_is_valid(ap_password)) {
        error = "Invalid AP password: 8-63 characters, no accents or emoji";
    } else if (hostname && hostname[0] && !wifi_manager_mdns_hostname_is_valid(hostname)) {
        error = "Invalid hostname: letters, digits and hyphens only, max 63";
    }

    if (error) {
        cJSON_Delete(json_req);
        httpd_resp_send_err(req, HTTPD_400_BAD_REQUEST, error);
        return ESP_FAIL;
    }

    // Everything was validated above, so a failure here is NVS failing to save
    esp_err_t ret = ESP_OK;
    if (ap_ssid) {
        ret = wifi_manager_set_ap_ssid(wifi, ap_ssid);
    }
    if (ret == ESP_OK && ap_password) {
        ret = wifi_manager_set_ap_password(wifi, ap_password);
    }
    if (ret == ESP_OK && hostname) {
        ret = wifi_manager_set_mdns_hostname(wifi, hostname);
    }

    cJSON_Delete(json_req);

    if (ret != ESP_OK) {
        httpd_resp_send_err(req, HTTPD_500_INTERNAL_SERVER_ERROR, "Failed to save settings");
        return ESP_FAIL;
    }

    httpd_resp_set_type(req, "application/json");

    JsonStreamWriter json(req);
    ret = json.beginObject();
    if (ret != ESP_OK) return ret;
    ret = json.write("success", true);
    if (ret != ESP_OK) return ret;
    ret = json.write("ap_ssid", wifi_manager_get_ap_ssid(wifi));
    if (ret != ESP_OK) return ret;
    ret = json.write("mdns_hostname", wifi_manager_get_mdns_hostname(wifi));
    if (ret != ESP_OK) return ret;
    ret = json.endObject();
    if (ret != ESP_OK) return ret;

    return json.finalize();
}

esp_err_t web_server_init(web_server_t *server, uint16_t port) {
    if (!server) {
        return ESP_ERR_INVALID_ARG;
    }

    memset(server, 0, sizeof(web_server_t));
    server->port = (port > 0) ? port : WEB_SERVER_PORT;
    server->initialized = true;
    asset_etag_init();
    g_server = server;

    ESP_LOGI(TAG, "Web server initialized on port %d", server->port);
    return ESP_OK;
}

esp_err_t web_server_start(web_server_t *server) {
    if (!server || !server->initialized) {
        return ESP_ERR_INVALID_STATE;
    }

    if (server->running) {
        ESP_LOGW(TAG, "Web server already running");
        return ESP_OK;
    }

    httpd_config_t config = HTTPD_DEFAULT_CONFIG();
    config.server_port = server->port;
    config.max_uri_handlers = sizeof(uri_handlers) / sizeof(uri_handlers[0]);
    config.max_open_sockets = 7;  // parallel asset + API fetches; see LWIP_MAX_SOCKETS in sdkconfig.defaults
    config.lru_purge_enable = true;

    esp_err_t ret = httpd_start(&server->server, &config);
    if (ret != ESP_OK) {
        ESP_LOGE(TAG, "Failed to start web server: %s", esp_err_to_name(ret));
        return ret;
    }

    // Register URI handlers
    for (int i = 0; i < sizeof(uri_handlers) / sizeof(uri_handlers[0]); i++) {
        ret = httpd_register_uri_handler(server->server, &uri_handlers[i]);
        if (ret != ESP_OK) {
            ESP_LOGE(TAG, "Failed to register URI handler for %s: %s",
                     uri_handlers[i].uri, esp_err_to_name(ret));
            httpd_stop(server->server);
            return ret;
        }
    }

    server->running = true;
    ESP_LOGI(TAG, "Web server started on port %d", server->port);
    return ESP_OK;
}

esp_err_t web_server_stop(web_server_t *server) {
    if (!server || !server->initialized) {
        return ESP_ERR_INVALID_STATE;
    }

    if (!server->running) {
        ESP_LOGW(TAG, "Web server not running");
        return ESP_OK;
    }

    esp_err_t ret = httpd_stop(server->server);
    if (ret != ESP_OK) {
        ESP_LOGE(TAG, "Failed to stop web server: %s", esp_err_to_name(ret));
        return ret;
    }

    server->server = NULL;
    server->running = false;
    ESP_LOGI(TAG, "Web server stopped");
    return ESP_OK;
}

esp_err_t web_server_deinit(web_server_t *server) {
    if (!server) {
        return ESP_ERR_INVALID_ARG;
    }

    if (server->running) {
        web_server_stop(server);
    }

    server->initialized = false;
    if (g_server == server) {
        g_server = NULL;
    }

    ESP_LOGI(TAG, "Web server deinitialized");
    return ESP_OK;
}

esp_err_t web_server_set_interface_context(web_server_t *server, interface_context_t *interface_ctx) {
    if (!server) {
        return ESP_ERR_INVALID_ARG;
    }

    server->interface_ctx = interface_ctx;
    return ESP_OK;
}

bool web_server_is_running(web_server_t *server) {
    if (!server) {
        return false;
    }
    return server->running;
}

uint16_t web_server_get_port(web_server_t *server) {
    if (!server) {
        return 0;
    }
    return server->port;
}

static esp_err_t api_firmware_check_handler(httpd_req_t *req) {
    httpd_resp_set_type(req, "application/json");

    JsonStreamWriter json(req);
    esp_err_t ret = json.beginObject();
    if (ret != ESP_OK) return ret;

    // Initialize OTA manager if needed
    if (g_server && g_server->interface_ctx && g_server->interface_ctx->host_comm) {
#ifdef CONFIG_PRODUCT_BLUESCSI
        ota_manager_init(&g_ota_manager, g_server->interface_ctx->host_comm);

        // Get current version
        uint32_t current_version = ota_manager_get_current_version();
        ret = json.write("current_version", current_version);
        if (ret != ESP_OK) return ret;

        // Check for update
        bool update_available = false;
        esp_err_t check_ret = ota_manager_check_update(&g_ota_manager, &update_available);

        if (check_ret == ESP_OK) {
            ret = json.write("update_available", update_available ? 1 : 0);
            if (ret != ESP_OK) return ret;

            // Include firmware info if a file is present (even if same version)
            if (g_ota_manager.firmware_info.available) {
                ret = json.write("available_version", g_ota_manager.firmware_info.version);
                if (ret != ESP_OK) return ret;

                ret = json.write("firmware_size", g_ota_manager.firmware_info.size);
                if (ret != ESP_OK) return ret;
            }
        } else {
            ret = json.write("current_version", 0);
            if (ret != ESP_OK) return ret;

            ret = json.write("update_available", 0);
            if (ret != ESP_OK) return ret;

            ret = json.write("error", esp_err_to_name(check_ret));
            if (ret != ESP_OK) return ret;
        }
#else
        host_comm_t *comm = g_server->interface_ctx->host_comm;

        // Get main board firmware status (user-facing "system version")
        rp2350_fw_status_t rp_status = {};
        esp_err_t rp_ret = host_comm_get_rp2350_fw_status(comm, &rp_status);

        if (rp_ret == ESP_OK) {
            ret = json.write("current_version", rp_status.current_version);
            if (ret != ESP_OK) return ret;

            // Check if any update is available (main board or panel)
            bool main_update = (rp_status.available_version != 0);

            // Also check panel firmware from combined UF2
            ota_manager_init(&g_ota_manager, comm);
            bool panel_update = false;
            panel_firmware_info_t panel_info = {};
            esp_err_t panel_ret = host_comm_check_firmware(comm, &panel_info);
            if (panel_ret == ESP_OK && panel_info.available) {
                uint32_t current_panel_ver = ota_manager_get_current_version();
                panel_update = (panel_info.version > current_panel_ver);
            }

            bool any_update = main_update || panel_update;
            ret = json.write("update_available", any_update ? 1 : 0);
            if (ret != ESP_OK) return ret;

            if (any_update) {
                ret = json.write("available_version", rp_status.available_version);
                if (ret != ESP_OK) return ret;
            }
        } else {
            ret = json.write("current_version", 0);
            if (ret != ESP_OK) return ret;

            ret = json.write("update_available", 0);
            if (ret != ESP_OK) return ret;

            ret = json.write("error", esp_err_to_name(rp_ret));
            if (ret != ESP_OK) return ret;
        }
#endif
    } else {
        ret = json.write("current_version", 0);
        if (ret != ESP_OK) return ret;

        ret = json.write("update_available", 0);
        if (ret != ESP_OK) return ret;

        ret = json.write("error", "Interface not available");
        if (ret != ESP_OK) return ret;
    }

    ret = json.endObject();
    if (ret != ESP_OK) return ret;

    return json.finalize();
}

#ifndef CONFIG_PRODUCT_BLUESCSI
// Unified update state tracking for web UI
typedef enum {
    WEB_UPDATE_IDLE = 0,
    WEB_UPDATE_PANEL,
    WEB_UPDATE_MAINBOARD,
    WEB_UPDATE_WAITING_REBOOT,
    WEB_UPDATE_SUCCESS,
    WEB_UPDATE_ERROR
} web_update_phase_t;

static volatile web_update_phase_t g_web_update_phase = WEB_UPDATE_IDLE;
static volatile uint8_t g_web_update_progress = 0;
static const char* g_web_update_error = NULL;

// Background task that runs the unified update flow
static void web_firmware_update_task(void *pvParameters) {
    host_comm_t *comm = (host_comm_t *)pvParameters;

    // Check what needs updating
    panel_firmware_info_t panel_info = {};
    esp_err_t ret = host_comm_check_firmware(comm, &panel_info);
    bool panel_needs_update = (ret == ESP_OK && panel_info.available &&
                               panel_info.version > ota_manager_get_current_version());

    rp2350_fw_status_t rp_status = {};
    ret = host_comm_get_rp2350_fw_status(comm, &rp_status);
    bool main_needs_update = (ret == ESP_OK && rp_status.available_version != 0);

    bool panel_ota_written = false;

    // Phase 1: Panel OTA (if needed)
    if (panel_needs_update) {
        g_web_update_phase = WEB_UPDATE_PANEL;
        g_web_update_progress = 0;

        ota_manager_init(&g_ota_manager, comm);
        memcpy(&g_ota_manager.firmware_info, &panel_info, sizeof(panel_firmware_info_t));

        ret = ota_manager_start_update(&g_ota_manager);
        if (ret != ESP_OK) {
            g_web_update_error = "Failed to start panel OTA";
            g_web_update_phase = WEB_UPDATE_ERROR;
            vTaskDelete(NULL);
            return;
        }

        while (1) {
            ret = ota_manager_process(&g_ota_manager);
            ota_state_t state = ota_manager_get_state(&g_ota_manager);
            g_web_update_progress = ota_manager_get_progress(&g_ota_manager);

            if (state == OTA_STATE_SUCCESS) {
                panel_ota_written = true;
                break;
            } else if (state == OTA_STATE_ERROR) {
                g_web_update_error = "Panel OTA failed";
                g_web_update_phase = WEB_UPDATE_ERROR;
                vTaskDelete(NULL);
                return;
            }
            taskYIELD();
        }
    }

    // Phase 2: Main board update
    if (main_needs_update) {
        g_web_update_phase = WEB_UPDATE_MAINBOARD;
        g_web_update_progress = 0;

        ret = host_comm_start_rp2350_update(comm);
        if (ret != ESP_OK) {
            g_web_update_error = "Failed to start main board update";
            if (panel_ota_written) {
                // Panel OTA was already written, reboot to apply it at least
                esp_restart();
            }
            g_web_update_phase = WEB_UPDATE_ERROR;
            vTaskDelete(NULL);
            return;
        }

        // Wait for main board to reboot
        g_web_update_phase = WEB_UPDATE_WAITING_REBOOT;
        g_web_update_progress = 50;

        // Give it time to flash and reboot
        vTaskDelay(pdMS_TO_TICKS(5000));

        // Poll for main board to come back
        for (int attempts = 0; attempts < 20; attempts++) {
            vTaskDelay(pdMS_TO_TICKS(500));
            rp2350_fw_status_t new_status;
            if (host_comm_get_rp2350_fw_status(comm, &new_status) == ESP_OK) {
                g_web_update_progress = 100;
                break;
            }
        }
    }

    // Phase 3: Reboot panel if OTA was written
    if (panel_ota_written) {
        g_web_update_phase = WEB_UPDATE_SUCCESS;
        g_web_update_progress = 100;
        vTaskDelay(pdMS_TO_TICKS(2000));
        esp_restart();
    }

    g_web_update_phase = WEB_UPDATE_SUCCESS;
    g_web_update_progress = 100;
    vTaskDelete(NULL);
}
#endif

#ifdef CONFIG_PRODUCT_BLUESCSI
static esp_err_t api_firmware_update_handler(httpd_req_t *req) {
    httpd_resp_set_type(req, "application/json");

    JsonStreamWriter json(req);
    esp_err_t ret = json.beginObject();
    if (ret != ESP_OK) return ret;

    bool success = false;
    if (g_ota_task_handle != NULL) {
        ret = json.write("error", "Update already in progress");
        if (ret != ESP_OK) return ret;
    } else if (g_server && g_server->interface_ctx && g_server->interface_ctx->host_comm) {
        esp_err_t update_ret = ota_manager_start_update(&g_ota_manager);
        success = (update_ret == ESP_OK);

        if (success) {
            // Start background task to process OTA
            BaseType_t task_ret = xTaskCreate(web_firmware_update_task, "web_ota",
                                              8192, &g_ota_manager, 10, &g_ota_task_handle);
            if (task_ret != pdPASS) {
                ESP_LOGE(TAG, "Failed to create OTA task");
                ota_manager_abort(&g_ota_manager);
                success = false;
                ret = json.write("error", "Failed to create update task");
                if (ret != ESP_OK) return ret;
            }
        } else {
            ret = json.write("error", esp_err_to_name(update_ret));
            if (ret != ESP_OK) return ret;
        }
    } else {
        ret = json.write("error", "Interface not available");
        if (ret != ESP_OK) return ret;
    }

    ret = json.write("success", success);
    if (ret != ESP_OK) return ret;

    ret = json.endObject();
    if (ret != ESP_OK) return ret;

    return json.finalize();
}
#else
// Unified firmware update trigger
static esp_err_t api_firmware_update_handler(httpd_req_t *req) {
    httpd_resp_set_type(req, "application/json");

    JsonStreamWriter json(req);
    esp_err_t ret = json.beginObject();
    if (ret != ESP_OK) return ret;

    bool success = false;
    if (g_server && g_server->interface_ctx && g_server->interface_ctx->host_comm &&
        g_web_update_phase == WEB_UPDATE_IDLE) {

        g_web_update_phase = WEB_UPDATE_PANEL;  // Will be adjusted by task
        g_web_update_progress = 0;
        g_web_update_error = NULL;

        BaseType_t task_ret = xTaskCreate(web_firmware_update_task, "web_fw_update", 8192,
                                          g_server->interface_ctx->host_comm, 10, NULL);
        success = (task_ret == pdPASS);

        if (!success) {
            g_web_update_phase = WEB_UPDATE_IDLE;
            ret = json.write("error", "Failed to create update task");
            if (ret != ESP_OK) return ret;
        }
    } else if (g_web_update_phase != WEB_UPDATE_IDLE) {
        ret = json.write("error", "Update already in progress");
        if (ret != ESP_OK) return ret;
    } else {
        ret = json.write("error", "Interface not available");
        if (ret != ESP_OK) return ret;
    }

    ret = json.write("success", success);
    if (ret != ESP_OK) return ret;

    ret = json.endObject();
    if (ret != ESP_OK) return ret;

    return json.finalize();
}
#endif

#ifdef CONFIG_PRODUCT_BLUESCSI
static esp_err_t api_firmware_status_handler(httpd_req_t *req) {
    httpd_resp_set_type(req, "application/json");

    JsonStreamWriter json(req);
    esp_err_t ret = json.beginObject();
    if (ret != ESP_OK) return ret;

    // OTA processing happens in background task (web_firmware_update_task),
    // so we just read the current state here without calling ota_manager_process.

    // Get current state
    ota_state_t state = ota_manager_get_state(&g_ota_manager);
    uint8_t progress = ota_manager_get_progress(&g_ota_manager);

    // Convert state to string
    const char* state_str;
    switch (state) {
        case OTA_STATE_IDLE:
            state_str = "idle";
            break;
        case OTA_STATE_CHECKING:
            state_str = "checking";
            break;
        case OTA_STATE_DOWNLOADING:
            state_str = "downloading";
            break;
        case OTA_STATE_VERIFYING:
            state_str = "verifying";
            break;
        case OTA_STATE_APPLYING:
            state_str = "applying";
            break;
        case OTA_STATE_SUCCESS:
            state_str = "success";
            break;
        case OTA_STATE_ERROR:
            state_str = "error";
            break;
        default:
            state_str = "unknown";
    }

    ret = json.write("state", state_str);
    if (ret != ESP_OK) return ret;

    ret = json.write("progress", progress);
    if (ret != ESP_OK) return ret;

    if (state == OTA_STATE_ERROR) {
        ret = json.write("error", esp_err_to_name(g_ota_manager.last_error));
        if (ret != ESP_OK) return ret;
    }

    ret = json.endObject();
    if (ret != ESP_OK) return ret;

    return json.finalize();
}
#else
// Unified firmware status
static esp_err_t api_firmware_status_handler(httpd_req_t *req) {
    httpd_resp_set_type(req, "application/json");

    JsonStreamWriter json(req);
    esp_err_t ret = json.beginObject();
    if (ret != ESP_OK) return ret;

    const char* state_str;
    switch (g_web_update_phase) {
        case WEB_UPDATE_IDLE:       state_str = "idle"; break;
        case WEB_UPDATE_PANEL:      state_str = "updating_panel"; break;
        case WEB_UPDATE_MAINBOARD:  state_str = "updating_mainboard"; break;
        case WEB_UPDATE_WAITING_REBOOT: state_str = "rebooting"; break;
        case WEB_UPDATE_SUCCESS:    state_str = "success"; break;
        case WEB_UPDATE_ERROR:      state_str = "error"; break;
        default:                    state_str = "unknown"; break;
    }

    ret = json.write("state", state_str);
    if (ret != ESP_OK) return ret;

    ret = json.write("progress", (uint32_t)g_web_update_progress);
    if (ret != ESP_OK) return ret;

    if (g_web_update_phase == WEB_UPDATE_ERROR && g_web_update_error) {
        ret = json.write("error", g_web_update_error);
        if (ret != ESP_OK) return ret;
    }

    // Reset to idle after client reads success/error
    if (g_web_update_phase == WEB_UPDATE_SUCCESS || g_web_update_phase == WEB_UPDATE_ERROR) {
        g_web_update_phase = WEB_UPDATE_IDLE;
    }

    ret = json.endObject();
    if (ret != ESP_OK) return ret;

    return json.finalize();
}
#endif

#ifdef CONFIG_PRODUCT_BLUESCSI
// Mainboard (RP2350) firmware tracking state
static bool g_mainboard_update_started = false;

static esp_err_t api_mainboard_firmware_check_handler(httpd_req_t *req) {
    httpd_resp_set_type(req, "application/json");

    JsonStreamWriter json(req);
    esp_err_t ret = json.beginObject();
    if (ret != ESP_OK) return ret;

    if (g_server && g_server->interface_ctx && g_server->interface_ctx->host_comm) {
        rp2350_fw_status_t status;
        esp_err_t check_ret = host_comm_get_rp2350_fw_status(g_server->interface_ctx->host_comm, &status);

        if (check_ret == ESP_OK) {
            ret = json.write("current_version", status.current_version);
            if (ret != ESP_OK) return ret;

            bool update_available = (status.available_version != 0);
            ret = json.write("update_available", update_available ? 1 : 0);
            if (ret != ESP_OK) return ret;

            if (update_available) {
                ret = json.write("available_version", status.available_version);
                if (ret != ESP_OK) return ret;
            }
        } else {
            ret = json.write("current_version", 0);
            if (ret != ESP_OK) return ret;

            ret = json.write("update_available", 0);
            if (ret != ESP_OK) return ret;

            ret = json.write("error", esp_err_to_name(check_ret));
            if (ret != ESP_OK) return ret;
        }
    } else {
        ret = json.write("current_version", 0);
        if (ret != ESP_OK) return ret;

        ret = json.write("update_available", 0);
        if (ret != ESP_OK) return ret;

        ret = json.write("error", "Interface not available");
        if (ret != ESP_OK) return ret;
    }

    ret = json.endObject();
    if (ret != ESP_OK) return ret;

    return json.finalize();
}

// For PicoIDE: main board firmware is read from SD card by the RP2350, updated via SPI command.
// For BlueSCSI: main board firmware is uploaded via web UI to SD card, then applied on reboot.
static esp_err_t api_mainboard_firmware_update_handler(httpd_req_t *req) {
    httpd_resp_set_type(req, "application/json");

    JsonStreamWriter json(req);
    esp_err_t ret = json.beginObject();
    if (ret != ESP_OK) return ret;

    bool success = false;
    if (g_server && g_server->interface_ctx && g_server->interface_ctx->host_comm) {
        esp_err_t update_ret = host_comm_start_rp2350_update(g_server->interface_ctx->host_comm);
        success = (update_ret == ESP_OK);

        if (success) {
            g_mainboard_update_started = true;
        } else {
            ret = json.write("error", esp_err_to_name(update_ret));
            if (ret != ESP_OK) return ret;
        }
    } else {
        ret = json.write("error", "Interface not available");
        if (ret != ESP_OK) return ret;
    }

    ret = json.write("success", success);
    if (ret != ESP_OK) return ret;

    ret = json.endObject();
    if (ret != ESP_OK) return ret;

    return json.finalize();
}

static esp_err_t api_mainboard_firmware_status_handler(httpd_req_t *req) {
    httpd_resp_set_type(req, "application/json");

    JsonStreamWriter json(req);
    esp_err_t ret = json.beginObject();
    if (ret != ESP_OK) return ret;

    if (g_server && g_server->interface_ctx && g_server->interface_ctx->host_comm) {
        panel_command_status_t cmd_status;
        esp_err_t status_ret = host_comm_get_command_status(g_server->interface_ctx->host_comm, &cmd_status);

        if (status_ret == ESP_OK) {
            // Determine state string based on async state
            const char* state_str;
            switch (cmd_status.state) {
                case PANEL_ASYNC_IDLE:
                    state_str = g_mainboard_update_started ? "rebooting" : "idle";
                    break;
                case PANEL_ASYNC_PROCESSING:
                    state_str = "updating";
                    break;
                case PANEL_ASYNC_READY:
                    state_str = "success";
                    g_mainboard_update_started = false;
                    break;
                case PANEL_ASYNC_ERROR:
                    state_str = "error";
                    g_mainboard_update_started = false;
                    break;
                default:
                    state_str = "unknown";
            }

            ret = json.write("state", state_str);
            if (ret != ESP_OK) return ret;

            ret = json.write("progress", cmd_status.progress);
            if (ret != ESP_OK) return ret;

            if (cmd_status.state == PANEL_ASYNC_ERROR) {
                ret = json.write("error", "Update failed");
                if (ret != ESP_OK) return ret;
            }
        } else {
            // Communication lost - board may be rebooting
            if (g_mainboard_update_started) {
                ret = json.write("state", "rebooting");
                if (ret != ESP_OK) return ret;

                ret = json.write("progress", 100);
                if (ret != ESP_OK) return ret;
            } else {
                ret = json.write("state", "error");
                if (ret != ESP_OK) return ret;

                ret = json.write("progress", 0);
                if (ret != ESP_OK) return ret;

                ret = json.write("error", "Communication lost");
                if (ret != ESP_OK) return ret;
            }
        }
    } else {
        ret = json.write("state", "error");
        if (ret != ESP_OK) return ret;

        ret = json.write("progress", 0);
        if (ret != ESP_OK) return ret;

        ret = json.write("error", "Interface not available");
        if (ret != ESP_OK) return ret;
    }

    ret = json.endObject();
    if (ret != ESP_OK) return ret;

    return json.finalize();
}
#endif // #ifdef CONFIG_PRODUCT_BLUESCSI

// File upload state
typedef struct {
    char filename[256];
    char target_path[512];
    uint32_t total_size;
    uint32_t bytes_received;
    bool upload_started;
    bool upload_finished;
} upload_state_t;

static upload_state_t g_upload_state = {
    .filename = {0},
    .target_path = {0},
    .total_size = 0,
    .bytes_received = 0,
    .upload_started = false,
    .upload_finished = false
};

static inline char* strnmem(const void* haystack, const char* needle, size_t haystacklen) {
    return (char *)memmem(haystack, haystacklen, needle, strlen(needle));
}

// Parse the first chunk of a multipart/form-data body for the {fileSize,
// fileData} fields the web UI sends. On success returns ESP_OK and fills
// filename, *file_size, and *file_data_start (offset of the file payload
// within buf, 0 if the payload hasn't started in this chunk). On failure
// returns ESP_FAIL and points *err_msg at a static reason string.
static esp_err_t parse_upload_multipart_header(const char *buf, int received,
                                               char *filename, size_t filename_size,
                                               uint32_t *file_size,
                                               uint32_t *file_data_start,
                                               const char **err_msg) {
    *file_size = 0;
    *file_data_start = 0;
    filename[0] = '\0';
    bool found_file_size = false;

    // fileSize field
    char *filesize_field = strnmem(buf, "name=\"fileSize\"", received);
    if (filesize_field) {
        char *value_start = strnmem(filesize_field, "\r\n\r\n", received - (filesize_field - buf));
        if (value_start) {
            value_start += 4; // Skip \r\n\r\n
            char *value_end = strnmem(value_start, "\r\n--", received - (value_start - buf));
            if (value_end) {
                char size_str[32] = {0};
                size_t size_len = value_end - value_start;
                if (size_len < sizeof(size_str)) {
                    strncpy(size_str, value_start, size_len);
                    *file_size = strtoul(size_str, NULL, 10);
                    found_file_size = true;
                }
            }
        }
    }

    // filename in the fileData field
    char *filename_start = NULL;
    char *filedata_field = strnmem(buf, "name=\"fileData\"", received);
    if (filedata_field) {
        filename_start = strnmem(filedata_field, "filename=\"", received - (filedata_field - buf));
    }
    if (filename_start) {
        filename_start += 10; // Skip 'filename="'
        char *filename_end = strchr(filename_start, '"');
        if (filename_end) {
            size_t filename_len = filename_end - filename_start;
            if (filename_len < filename_size) {
                strncpy(filename, filename_start, filename_len);
                filename[filename_len] = '\0';
            }
        }
    }

    if (filename[0] == '\0') {
        *err_msg = "Invalid multipart data - missing filename";
        return ESP_FAIL;
    }
    if (!found_file_size) {
        *err_msg = "Invalid multipart data - missing file size";
        return ESP_FAIL;
    }

    // Start of file payload (after the file field headers)
    char *data_start = strnmem(filename_start, "\r\n\r\n", received - (filename_start - buf));
    if (data_start) {
        data_start += 4; // Skip \r\n\r\n
        *file_data_start = data_start - buf;
    }
    return ESP_OK;
}

// Error replies during an upload. The browser is still streaming the request
// body when a handler rejects it, so responding immediately makes
// esp_http_server drop the socket and the browser reports a generic network
// error with the message never read. Read the rest of the body first.
static esp_err_t upload_error(httpd_req_t *req, const char *status, const char *msg) {
    char drain[512];
    while (httpd_req_recv(req, drain, sizeof(drain)) > 0) {
    }
    httpd_resp_set_status(req, status);
    httpd_resp_send(req, msg, HTTPD_RESP_USE_STRLEN);
    return ESP_FAIL;
}

static esp_err_t handle_file_upload(httpd_req_t *req, const char *path_prefix) {
    ESP_LOGI(TAG, "Upload request received (prefix: \"%s\")", path_prefix);

    // Reset upload state
    memset(&g_upload_state, 0, sizeof(g_upload_state));

    // Get content length
    size_t content_length = req->content_len;
    if (content_length == 0) {
        ESP_LOGE(TAG, "No content in upload request");
        return upload_error(req, "400 Bad Request", "No content");
    }

    ESP_LOGI(TAG, "Upload content length: %u bytes", content_length);

    // Allocate buffer for reading chunks (match protocol chunk size)
    const size_t chunk_size = PANEL_FILE_CHUNK_SIZE;
    char *chunk_buffer = (char*)malloc(chunk_size);
    if (!chunk_buffer) {
        ESP_LOGE(TAG, "Failed to allocate upload buffer");
        return upload_error(req, "500 Internal Server Error", "Memory allocation failed");
    }

    uint32_t actual_file_size = 0;
    uint32_t file_data_start = 0;

    // Read first chunk to parse headers
    int received = httpd_req_recv(req, chunk_buffer, chunk_size);
    if (received <= 0) {
        ESP_LOGE(TAG, "Failed to receive upload data");
        free(chunk_buffer);
        return upload_error(req, "400 Bad Request", "Failed to receive data");
    }

    // Parse multipart headers (filename + file size) from the first chunk
    const char *parse_err = NULL;
    if (parse_upload_multipart_header(chunk_buffer, received,
                                      g_upload_state.filename, sizeof(g_upload_state.filename),
                                      &actual_file_size, &file_data_start, &parse_err) != ESP_OK) {
        ESP_LOGE(TAG, "%s", parse_err);
        free(chunk_buffer);
        return upload_error(req, "400 Bad Request", parse_err);
    }
    ESP_LOGI(TAG, "Upload: %s (%u bytes), data at offset %u",
             g_upload_state.filename, actual_file_size, file_data_start);

    // Set target path using path_prefix + filename
    snprintf(g_upload_state.target_path, sizeof(g_upload_state.target_path),
             "%s%s", path_prefix, g_upload_state.filename);

    // Start file upload to RP2350
    if (!g_server || !g_server->interface_ctx->host_comm) {
        ESP_LOGE(TAG, "Host communication not available");
        free(chunk_buffer);
        return upload_error(req, "503 Service Unavailable", "Host not connected");
    }

    host_comm_t *host_comm = g_server->interface_ctx->host_comm;

    // Start file upload on RP2350 with actual file size
    esp_err_t ret = host_comm_start_file_upload(host_comm, g_upload_state.target_path, actual_file_size);
    if (ret != ESP_OK) {
        ESP_LOGE(TAG, "Failed to start file upload: %s", esp_err_to_name(ret));
        free(chunk_buffer);
        return upload_error(req, "500 Internal Server Error", "Failed to start upload");
    }

    // Process file data from the first chunk
    if (file_data_start > 0 && (uint32_t)file_data_start < (uint32_t)received) {
        size_t first_chunk_data_size = received - file_data_start;
        // Cap at actual file size (don't include trailing multipart boundary for small files)
        if (first_chunk_data_size > actual_file_size) {
            first_chunk_data_size = actual_file_size;
        }
        ESP_LOGI(TAG, "Processing first chunk data: %d bytes", first_chunk_data_size);

        if (first_chunk_data_size > PANEL_FILE_CHUNK_SIZE) {
            ESP_LOGE(TAG, "First chunk data too large: %d bytes (max %d)",
                     first_chunk_data_size, PANEL_FILE_CHUNK_SIZE);
            free(chunk_buffer);
            return upload_error(req, "400 Bad Request", "Multipart header too large");
        }

        ret = host_comm_write_file_chunk(host_comm,
                                        (uint8_t*)(chunk_buffer + file_data_start),
                                        first_chunk_data_size);
        if (ret != ESP_OK) {
            ESP_LOGE(TAG, "Failed to write first chunk: %s", esp_err_to_name(ret));
            free(chunk_buffer);
            return upload_error(req, "500 Internal Server Error", "Upload failed");
        }

        g_upload_state.bytes_received += first_chunk_data_size;
    }

    // Calculate how much file data remains after first chunk
    size_t remaining = actual_file_size - g_upload_state.bytes_received;
    while (remaining > 0) {
        size_t to_read = (remaining > chunk_size) ? chunk_size : remaining;

        int chunk_received = httpd_req_recv(req, chunk_buffer, to_read);
        if (chunk_received <= 0) {
            ESP_LOGE(TAG, "Failed to receive chunk data");
            free(chunk_buffer);
            return upload_error(req, "400 Bad Request", "Failed to receive data");
        }

        // Write chunk to RP2350
        ret = host_comm_write_file_chunk(host_comm, (uint8_t*)chunk_buffer, chunk_received);
        if (ret != ESP_OK) {
            ESP_LOGE(TAG, "Failed to write chunk: %s", esp_err_to_name(ret));
            free(chunk_buffer);
            return upload_error(req, "500 Internal Server Error", "Upload failed");
        }

        g_upload_state.bytes_received += chunk_received;

        remaining -= chunk_received;

        ESP_LOGD(TAG, "Uploaded %u / %u bytes", g_upload_state.bytes_received, actual_file_size);
    }

    // Finish the upload and get file hash
    uint8_t upload_result;
    uint8_t file_hash[32];
    ret = host_comm_finish_file_upload(host_comm, &upload_result, file_hash);
    interface_invalidate_disc_list();
    if (ret != ESP_OK) {
        ESP_LOGE(TAG, "Failed to finish upload: %s", esp_err_to_name(ret));
        free(chunk_buffer);
        return upload_error(req, "500 Internal Server Error", "Upload failed");
    }

    free(chunk_buffer);

    // Check upload result
    if (upload_result != PANEL_UPLOAD_OK) {
        ESP_LOGE(TAG, "Upload failed on RP2350 with code: 0x%02X", upload_result);
        httpd_resp_set_status(req, "500 Internal Server Error");

        const char* error_msg;
        switch (upload_result) {
            case PANEL_UPLOAD_ERROR_DISK:
                error_msg = "Disk error";
                break;
            case PANEL_UPLOAD_ERROR_SPACE:
                error_msg = "Insufficient space";
                break;
            case PANEL_UPLOAD_ERROR_WRITE:
                error_msg = "Write error";
                break;
            case PANEL_UPLOAD_ERROR_PATH:
                error_msg = "Invalid path";
                break;
            default:
                error_msg = "Unknown error";
        }

        httpd_resp_send(req, error_msg, HTTPD_RESP_USE_STRLEN);
        return ESP_FAIL;
    }

    // Convert hash to hex string
    char hash_hex[65];
    for (int i = 0; i < 32; i++) {
        snprintf(hash_hex + (i * 2), sizeof(hash_hex) - (i * 2), "%02x", file_hash[i]);
    }
    hash_hex[64] = '\0';

    ESP_LOGI(TAG, "File upload completed successfully: %s (%u bytes), SHA256: %s",
             g_upload_state.target_path, g_upload_state.bytes_received, hash_hex);

    // Send success response with hash
    httpd_resp_set_type(req, "application/json");

    JsonStreamWriter json(req);
    ret = json.beginObject();
    if (ret != ESP_OK) return ret;

    ret = json.write("success", true);
    if (ret != ESP_OK) return ret;

    ret = json.write("filename", g_upload_state.filename);
    if (ret != ESP_OK) return ret;

    ret = json.write("path", g_upload_state.target_path);
    if (ret != ESP_OK) return ret;

    ret = json.write("size", (int)g_upload_state.bytes_received);
    if (ret != ESP_OK) return ret;

    ret = json.write("hash", hash_hex);
    if (ret != ESP_OK) return ret;

    ret = json.endObject();
    if (ret != ESP_OK) return ret;

    return json.finalize();
}

// Thin wrapper: regular file upload (JS sends full path in filename)
static esp_err_t api_upload_handler(httpd_req_t *req) {
    return handle_file_upload(req, "");
}

#ifdef CONFIG_PRODUCT_BLUESCSI
// Thin wrapper: mainboard firmware upload (prefix "/" to ensure root path)
static esp_err_t api_mainboard_firmware_upload_handler(httpd_req_t *req) {
    return handle_file_upload(req, "/");
}

// Reboot shortly after the HTTP response is flushed, so the freshly written
// OTA image becomes active.
static void panel_reboot_task(void *pvParameters) {
    vTaskDelay(pdMS_TO_TICKS(2000));
    ESP_LOGI(TAG, "Rebooting to apply uploaded panel firmware...");
    esp_restart();
}

// esp_ota_write() rejects the first block when the file is not an app image,
// which is what uploading bootloader.bin or partition-table.bin looks like.
static esp_err_t ota_write_error(httpd_req_t *req, esp_err_t err) {
    if (err == ESP_ERR_OTA_VALIDATE_FAILED) {
        return upload_error(req, "400 Bad Request",
                            "That file is not panel firmware");
    }
    return upload_error(req, "500 Internal Server Error", "OTA write failed");
}

// Direct ESP32 panel firmware upload: stream the posted .bin straight into the
// next OTA partition (no SD card / main board round-trip), then reboot. This is
// the front-panel counterpart to api_mainboard_firmware_upload_handler.
static esp_err_t api_panel_firmware_upload_handler(httpd_req_t *req) {
    // Don't collide with the SD-card-based panel OTA background task.
    if (g_ota_task_handle != NULL) {
        return upload_error(req, "409 Conflict", "Update already in progress");
    }

    if (req->content_len == 0) {
        return upload_error(req, "400 Bad Request", "No content");
    }

    const size_t chunk_size = PANEL_FILE_CHUNK_SIZE;
    char *chunk_buffer = (char *)malloc(chunk_size);
    if (!chunk_buffer) {
        return upload_error(req, "500 Internal Server Error", "Memory allocation failed");
    }

    int received = httpd_req_recv(req, chunk_buffer, chunk_size);
    if (received <= 0) {
        free(chunk_buffer);
        return upload_error(req, "400 Bad Request", "Failed to receive data");
    }

    char filename[256];
    uint32_t firmware_size = 0;
    uint32_t file_data_start = 0;
    const char *parse_err = NULL;
    if (parse_upload_multipart_header(chunk_buffer, received, filename, sizeof(filename),
                                      &firmware_size, &file_data_start, &parse_err) != ESP_OK) {
        ESP_LOGE(TAG, "%s", parse_err);
        free(chunk_buffer);
        return upload_error(req, "400 Bad Request", parse_err);
    }
    ESP_LOGI(TAG, "Panel firmware upload: %s (%u bytes)", filename, firmware_size);

    const esp_partition_t *update_partition = esp_ota_get_next_update_partition(NULL);
    if (!update_partition) {
        free(chunk_buffer);
        return upload_error(req, "500 Internal Server Error", "No OTA partition available");
    }

    esp_ota_handle_t ota_handle = 0;
    esp_err_t ret = esp_ota_begin(update_partition, firmware_size, &ota_handle);
    if (ret != ESP_OK) {
        ESP_LOGE(TAG, "esp_ota_begin failed: %s", esp_err_to_name(ret));
        free(chunk_buffer);
        return upload_error(req, "500 Internal Server Error", "Failed to begin OTA");
    }

    uint32_t bytes_written = 0;

    // File payload bytes that already arrived in the first (header) chunk.
    if (file_data_start > 0 && (uint32_t)file_data_start < (uint32_t)received) {
        size_t first_size = received - file_data_start;
        if (first_size > firmware_size) first_size = firmware_size;
        ret = esp_ota_write(ota_handle, chunk_buffer + file_data_start, first_size);
        if (ret != ESP_OK) {
            ESP_LOGE(TAG, "esp_ota_write failed: %s", esp_err_to_name(ret));
            esp_ota_abort(ota_handle);
            free(chunk_buffer);
            return ota_write_error(req, ret);
        }
        bytes_written += first_size;
    }

    // Stream the remaining firmware bytes (capped at firmware_size so the
    // trailing multipart boundary is never written into flash).
    while (bytes_written < firmware_size) {
        size_t remaining = firmware_size - bytes_written;
        size_t to_read = (remaining > chunk_size) ? chunk_size : remaining;
        int n = httpd_req_recv(req, chunk_buffer, to_read);
        if (n <= 0) {
            ESP_LOGE(TAG, "Failed to receive firmware data at %u/%u", bytes_written, firmware_size);
            esp_ota_abort(ota_handle);
            free(chunk_buffer);
            return upload_error(req, "400 Bad Request", "Failed to receive data");
        }
        ret = esp_ota_write(ota_handle, chunk_buffer, n);
        if (ret != ESP_OK) {
            ESP_LOGE(TAG, "esp_ota_write failed: %s", esp_err_to_name(ret));
            esp_ota_abort(ota_handle);
            free(chunk_buffer);
            return ota_write_error(req, ret);
        }
        bytes_written += n;
    }

    free(chunk_buffer);

    // esp_ota_end validates the image (magic byte, checksum, signature).
    ret = esp_ota_end(ota_handle);
    if (ret != ESP_OK) {
        ESP_LOGE(TAG, "esp_ota_end failed: %s", esp_err_to_name(ret));
        const char *msg = (ret == ESP_ERR_OTA_VALIDATE_FAILED)
            ? "That file is not panel firmware" : "OTA finalize failed";
        return upload_error(req, "400 Bad Request", msg);
    }

    ret = esp_ota_set_boot_partition(update_partition);
    if (ret != ESP_OK) {
        ESP_LOGE(TAG, "esp_ota_set_boot_partition failed: %s", esp_err_to_name(ret));
        return upload_error(req, "500 Internal Server Error", "Failed to set boot partition");
    }

    ESP_LOGI(TAG, "Panel firmware uploaded (%u bytes), rebooting", bytes_written);

    httpd_resp_set_type(req, "application/json");
    JsonStreamWriter json(req);
    ret = json.beginObject();
    if (ret != ESP_OK) return ret;
    ret = json.write("success", true);
    if (ret != ESP_OK) return ret;
    ret = json.write("size", (int)bytes_written);
    if (ret != ESP_OK) return ret;
    ret = json.endObject();
    if (ret != ESP_OK) return ret;
    ret = json.finalize();
    if (ret != ESP_OK) return ret;

    // Reboot once the response has been flushed to the client.
    xTaskCreate(panel_reboot_task, "panel_reboot", 2048, NULL, 5, NULL);
    return ESP_OK;
}
#endif

// Decode percent-encoding (and '+' as space) in place. httpd_query_key_value()
// returns the raw query value without decoding, so callers that send
// encodeURIComponent()'d values (e.g. paths with '/' as %2F) must decode here.
static void url_decode_inplace(char *s) {
    char *src = s, *dst = s;
    while (*src) {
        if (*src == '%' && isxdigit((unsigned char)src[1]) && isxdigit((unsigned char)src[2])) {
            char hex[3] = { src[1], src[2], '\0' };
            *dst++ = (char)strtol(hex, NULL, 16);
            src += 3;
        } else if (*src == '+') {
            *dst++ = ' ';
            src++;
        } else {
            *dst++ = *src++;
        }
    }
    *dst = '\0';
}

#ifdef CONFIG_PRODUCT_BLUESCSI
// Map a PANEL_DELETE_* result code to a user-facing message (NULL means success).
static const char *delete_error_string(uint8_t code) {
    switch (code) {
        case PANEL_DELETE_OK:              return NULL;
        case PANEL_DELETE_ERROR_NOT_FOUND: return "File not found";
        case PANEL_DELETE_ERROR_IN_USE:    return "File is currently loaded — eject it first";
        case PANEL_DELETE_ERROR_PATH:      return "Invalid path";
        case PANEL_DELETE_ERROR_IO:        return "Failed to delete file";
        default:                           return "Delete failed";
    }
}

// Map a PANEL_RENAME_* result code to a user-facing message (NULL means success).
static const char *rename_error_string(uint8_t code) {
    switch (code) {
        case PANEL_RENAME_OK:              return NULL;
        case PANEL_RENAME_ERROR_NOT_FOUND: return "File not found";
        case PANEL_RENAME_ERROR_EXISTS:    return "A file with that name already exists";
        case PANEL_RENAME_ERROR_IN_USE:    return "File is currently loaded — eject it first";
        case PANEL_RENAME_ERROR_PATH:      return "Invalid path";
        case PANEL_RENAME_ERROR_IO:        return "Failed to rename file";
        default:                           return "Rename failed";
    }
}

// Delete handler - removes a file from the main board SD card.
// Usage: POST /api/delete  body: { "path": "/dir/image.iso" }
static esp_err_t api_delete_handler(httpd_req_t *req) {
    if (!g_server || !g_server->interface_ctx || !g_server->interface_ctx->host_comm) {
        httpd_resp_send_err(req, HTTPD_500_INTERNAL_SERVER_ERROR, "Host communication not available");
        return ESP_FAIL;
    }

    char content[512];
    size_t recv_size = MIN(req->content_len, sizeof(content) - 1);
    int ret = httpd_req_recv(req, content, recv_size);
    if (ret <= 0) {
        httpd_resp_send_500(req);
        return ESP_FAIL;
    }
    content[ret] = '\0';

    cJSON *json = cJSON_Parse(content);
    if (!json) {
        httpd_resp_send_err(req, HTTPD_400_BAD_REQUEST, "Invalid JSON");
        return ESP_FAIL;
    }

    cJSON *path_json = cJSON_GetObjectItem(json, "path");
    if (!cJSON_IsString(path_json) || path_json->valuestring[0] == '\0') {
        cJSON_Delete(json);
        httpd_resp_send_err(req, HTTPD_400_BAD_REQUEST, "Missing or invalid path");
        return ESP_FAIL;
    }

    ESP_LOGI(TAG, "Delete request for: %s", path_json->valuestring);

    uint8_t result_code = 0xFF;
    esp_err_t del_ret = host_comm_delete_file(g_server->interface_ctx->host_comm,
                                              path_json->valuestring, &result_code);
    interface_invalidate_disc_list();
    cJSON_Delete(json);

    httpd_resp_set_type(req, "application/json");
    JsonStreamWriter jw(req);
    esp_err_t jret = jw.beginObject();
    if (jret != ESP_OK) return jret;

    bool success = (del_ret == ESP_OK && result_code == PANEL_DELETE_OK);
    if (!success) {
        const char *msg = (del_ret != ESP_OK) ? "Communication error with main board"
                                              : delete_error_string(result_code);
        jret = jw.write("error", msg ? msg : "Delete failed");
        if (jret != ESP_OK) return jret;
    }
    jret = jw.write("success", success);
    if (jret != ESP_OK) return jret;
    jret = jw.endObject();
    if (jret != ESP_OK) return jret;
    return jw.finalize();
}

// Rename handler - renames a file on the main board SD card.
// Usage: POST /api/rename  body: { "old_path": "/a.iso", "new_path": "/b.iso" }
static esp_err_t api_rename_handler(httpd_req_t *req) {
    if (!g_server || !g_server->interface_ctx || !g_server->interface_ctx->host_comm) {
        httpd_resp_send_err(req, HTTPD_500_INTERNAL_SERVER_ERROR, "Host communication not available");
        return ESP_FAIL;
    }

    char content[768];
    size_t recv_size = MIN(req->content_len, sizeof(content) - 1);
    int ret = httpd_req_recv(req, content, recv_size);
    if (ret <= 0) {
        httpd_resp_send_500(req);
        return ESP_FAIL;
    }
    content[ret] = '\0';

    cJSON *json = cJSON_Parse(content);
    if (!json) {
        httpd_resp_send_err(req, HTTPD_400_BAD_REQUEST, "Invalid JSON");
        return ESP_FAIL;
    }

    cJSON *old_json = cJSON_GetObjectItem(json, "old_path");
    cJSON *new_json = cJSON_GetObjectItem(json, "new_path");
    if (!cJSON_IsString(old_json) || old_json->valuestring[0] == '\0' ||
        !cJSON_IsString(new_json) || new_json->valuestring[0] == '\0') {
        cJSON_Delete(json);
        httpd_resp_send_err(req, HTTPD_400_BAD_REQUEST, "Missing or invalid old_path/new_path");
        return ESP_FAIL;
    }

    ESP_LOGI(TAG, "Rename request: %s -> %s", old_json->valuestring, new_json->valuestring);

    uint8_t result_code = 0xFF;
    esp_err_t rn_ret = host_comm_rename_file(g_server->interface_ctx->host_comm,
                                             old_json->valuestring, new_json->valuestring,
                                             &result_code);
    interface_invalidate_disc_list();
    cJSON_Delete(json);

    httpd_resp_set_type(req, "application/json");
    JsonStreamWriter jw(req);
    esp_err_t jret = jw.beginObject();
    if (jret != ESP_OK) return jret;

    bool success = (rn_ret == ESP_OK && result_code == PANEL_RENAME_OK);
    if (!success) {
        const char *msg = (rn_ret != ESP_OK) ? "Communication error with main board"
                                             : rename_error_string(result_code);
        jret = jw.write("error", msg ? msg : "Rename failed");
        if (jret != ESP_OK) return jret;
    }
    jret = jw.write("success", success);
    if (jret != ESP_OK) return jret;
    jret = jw.endObject();
    if (jret != ESP_OK) return jret;
    return jw.finalize();
}

static const char *touch_error_string(uint8_t code) {
    switch (code) {
        case PANEL_TOUCH_OK:           return NULL;
        case PANEL_TOUCH_ERROR_EXISTS: return "A file or folder with that name already exists";
        case PANEL_TOUCH_ERROR_PATH:   return "Invalid name";
        case PANEL_TOUCH_ERROR_IO:     return "Failed to create file";
        default:                       return "Create failed";
    }
}

static const char *mkdir_error_string(uint8_t code) {
    switch (code) {
        case PANEL_MKDIR_OK:           return NULL;
        case PANEL_MKDIR_ERROR_EXISTS: return "A file or folder with that name already exists";
        case PANEL_MKDIR_ERROR_PATH:   return "Invalid name";
        case PANEL_MKDIR_ERROR_IO:     return "Failed to create folder";
        default:                       return "Create failed";
    }
}

// Shared body for the single-path create endpoints (touch / mkdir). Parses
// { "path": "..." }, calls op_fn, and writes a JSON success/error response.
static esp_err_t api_create_path_op(httpd_req_t *req,
                                    esp_err_t (*op_fn)(host_comm_t *, const char *, uint8_t *),
                                    const char *(*err_fn)(uint8_t)) {
    if (!g_server || !g_server->interface_ctx || !g_server->interface_ctx->host_comm) {
        httpd_resp_send_err(req, HTTPD_500_INTERNAL_SERVER_ERROR, "Host communication not available");
        return ESP_FAIL;
    }

    char content[512];
    size_t recv_size = MIN(req->content_len, sizeof(content) - 1);
    int ret = httpd_req_recv(req, content, recv_size);
    if (ret <= 0) {
        httpd_resp_send_500(req);
        return ESP_FAIL;
    }
    content[ret] = '\0';

    cJSON *json = cJSON_Parse(content);
    if (!json) {
        httpd_resp_send_err(req, HTTPD_400_BAD_REQUEST, "Invalid JSON");
        return ESP_FAIL;
    }

    cJSON *path_json = cJSON_GetObjectItem(json, "path");
    if (!cJSON_IsString(path_json) || path_json->valuestring[0] == '\0') {
        cJSON_Delete(json);
        httpd_resp_send_err(req, HTTPD_400_BAD_REQUEST, "Missing or invalid path");
        return ESP_FAIL;
    }

    ESP_LOGI(TAG, "Create-path request for: %s", path_json->valuestring);

    uint8_t result_code = 0xFF;
    esp_err_t op_ret = op_fn(g_server->interface_ctx->host_comm,
                             path_json->valuestring, &result_code);
    interface_invalidate_disc_list();
    cJSON_Delete(json);

    httpd_resp_set_type(req, "application/json");
    JsonStreamWriter jw(req);
    esp_err_t jret = jw.beginObject();
    if (jret != ESP_OK) return jret;

    bool success = (op_ret == ESP_OK && result_code == 0);
    if (!success) {
        const char *msg = (op_ret != ESP_OK) ? "Communication error with main board"
                                             : err_fn(result_code);
        jret = jw.write("error", msg ? msg : "Create failed");
        if (jret != ESP_OK) return jret;
    }
    jret = jw.write("success", success);
    if (jret != ESP_OK) return jret;
    jret = jw.endObject();
    if (jret != ESP_OK) return jret;
    return jw.finalize();
}

// Create an empty file. Usage: POST /api/touch  body: { "path": "/NE4.hda" }
static esp_err_t api_touch_handler(httpd_req_t *req) {
    return api_create_path_op(req, host_comm_touch_file, touch_error_string);
}

// Create a directory. Usage: POST /api/mkdir  body: { "path": "/CD3" }
static esp_err_t api_mkdir_handler(httpd_req_t *req) {
    return api_create_path_op(req, host_comm_mkdir, mkdir_error_string);
}
#endif // CONFIG_PRODUCT_BLUESCSI

// File download handler - downloads a file from the main board SD card
// Usage: GET /api/download?path=/picoide.ini
static esp_err_t api_download_handler(httpd_req_t *req) {
    if (!g_server || !g_server->interface_ctx || !g_server->interface_ctx->host_comm) {
        httpd_resp_send_err(req, HTTPD_500_INTERNAL_SERVER_ERROR, "Host communication not available");
        return ESP_FAIL;
    }

    host_comm_t *host_comm = g_server->interface_ctx->host_comm;

    // Get the path query parameter
    char path[256] = {0};
    size_t query_len = httpd_req_get_url_query_len(req);
    if (query_len == 0) {
        httpd_resp_send_err(req, HTTPD_400_BAD_REQUEST, "Missing path parameter");
        return ESP_FAIL;
    }

    char *query_str = (char *)malloc(query_len + 1);
    if (!query_str) {
        httpd_resp_send_err(req, HTTPD_500_INTERNAL_SERVER_ERROR, "Memory allocation failed");
        return ESP_FAIL;
    }

    esp_err_t ret = httpd_req_get_url_query_str(req, query_str, query_len + 1);
    if (ret != ESP_OK) {
        free(query_str);
        httpd_resp_send_err(req, HTTPD_400_BAD_REQUEST, "Failed to get query string");
        return ESP_FAIL;
    }

    ret = httpd_query_key_value(query_str, "path", path, sizeof(path));
    free(query_str);
    if (ret != ESP_OK) {
        httpd_resp_send_err(req, HTTPD_400_BAD_REQUEST, "Missing or invalid path parameter");
        return ESP_FAIL;
    }

    // httpd_query_key_value() does not decode percent-encoding; the client sends
    // the path via encodeURIComponent(), so '/' arrives as %2F, etc.
    url_decode_inplace(path);

    ESP_LOGI(TAG, "Download request for: %s", path);

    // Start the file download
    uint32_t file_size = 0;
    ret = host_comm_start_file_download(host_comm, path, &file_size);
    if (ret != ESP_OK) {
        ESP_LOGE(TAG, "Failed to start file download: %s", esp_err_to_name(ret));
        httpd_resp_send_err(req, HTTPD_404_NOT_FOUND, "File not found");
        return ESP_FAIL;
    }

    ESP_LOGI(TAG, "Downloading file: %s (%" PRIu32 " bytes)", path, file_size);

    // Set content type based on file extension
    const char *ext = strrchr(path, '.');
    if (ext && strcasecmp(ext, ".ini") == 0) {
        httpd_resp_set_type(req, "text/plain; charset=utf-8");
    } else {
        httpd_resp_set_type(req, "application/octet-stream");
    }

    // Set content length
    char content_length[32];
    snprintf(content_length, sizeof(content_length), "%" PRIu32, file_size);
    httpd_resp_set_hdr(req, "Content-Length", content_length);

    // Read and send file in chunks
    uint8_t *chunk_buffer = (uint8_t *)malloc(PANEL_FILE_CHUNK_SIZE);
    if (!chunk_buffer) {
        httpd_resp_send_err(req, HTTPD_500_INTERNAL_SERVER_ERROR, "Memory allocation failed");
        return ESP_FAIL;
    }

    uint32_t bytes_sent = 0;
    uint32_t chunk_index = 0;

    while (bytes_sent < file_size) {
        size_t bytes_read = 0;
        ret = host_comm_read_file_chunk(host_comm, chunk_index, chunk_buffer, &bytes_read);
        if (ret != ESP_OK) {
            ESP_LOGE(TAG, "Failed to read file chunk %" PRIu32 ": %s", chunk_index, esp_err_to_name(ret));
            free(chunk_buffer);
            return ESP_FAIL;
        }

        if (bytes_read == 0) {
            break;  // End of file
        }

        ret = httpd_resp_send_chunk(req, (const char *)chunk_buffer, bytes_read);
        if (ret != ESP_OK) {
            ESP_LOGE(TAG, "Failed to send chunk: %s", esp_err_to_name(ret));
            free(chunk_buffer);
            return ESP_FAIL;
        }

        bytes_sent += bytes_read;
        chunk_index++;
    }

    free(chunk_buffer);

    // Send final empty chunk to signal end of response
    httpd_resp_send_chunk(req, NULL, 0);

    ESP_LOGI(TAG, "Download complete: %" PRIu32 " bytes sent", bytes_sent);
    return ESP_OK;
}
