polpo/open-retro-storage-frontpanel/sw-frontpanel/main/host_comm.c

// SPDX-License-Identifier: GPL-2.0-only
//
//  Copyright (C) 2025  Ian Scott
//
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
#include "host_comm.h"
#include "panel_protocol_defs.h"
#include "esp_log.h"
#include "esp_rom_crc.h"
#include "freertos/FreeRTOS.h"
#include "freertos/task.h"
#include <string.h>
#include <stdalign.h>

static const char *TAG = "host_comm";

// Mutex timeout for transport operations (30 seconds to allow long file operations)
#define HOST_COMM_MUTEX_TIMEOUT_MS 30000

// Helper macros for mutex handling
#define HOST_COMM_LOCK(comm) \
    if (xSemaphoreTake((comm)->mutex, pdMS_TO_TICKS(HOST_COMM_MUTEX_TIMEOUT_MS)) != pdTRUE) { \
        ESP_LOGE(TAG, "Failed to acquire mutex"); \
        return ESP_ERR_TIMEOUT; \
    }

#define HOST_COMM_UNLOCK(comm) xSemaphoreGive((comm)->mutex)

// Static buffers for zero-copy operations
alignas(4) static uint8_t tx_buffer[PANEL_PROTOCOL_MAX_PAYLOAD];
alignas(4) static uint8_t rx_buffer[PANEL_PROTOCOL_MAX_PAYLOAD];

// A live handle is one with a mutex: host_comm_init() creates it and
// host_comm_deinit() deletes it and leaves it NULL. That is the only thing the
// entry points below need to check before locking. comm->link_up answers a
// different question - whether the main board is answering - and main.c clears
// it while the handle stays up, so the reconnect path can keep calling through
// this API to find out when the board comes back.
static inline bool host_comm_have_handle(const host_comm_t *comm) {
    return comm && comm->mutex;
}

esp_err_t host_comm_init(host_comm_t *comm, const transport_config_t *config) {
    if (!comm || !config) {
        return ESP_ERR_INVALID_ARG;
    }

    // Create mutex for thread-safe access
    comm->mutex = xSemaphoreCreateMutex();
    if (!comm->mutex) {
        ESP_LOGE(TAG, "Failed to create mutex");
        return ESP_ERR_NO_MEM;
    }

    // Initialize transport layer
    esp_err_t ret = transport_init(&comm->transport, config);
    if (ret != ESP_OK) {
        ESP_LOGE(TAG, "Failed to initialize transport: %s", esp_err_to_name(ret));
        vSemaphoreDelete(comm->mutex);
        comm->mutex = NULL;
        return ret;
    }

    comm->link_up = true;

    ESP_LOGI(TAG, "Host communication initialized using %s transport (device addr: 0x%02X)",
             transport_get_name(&comm->transport), config->device_addr);

    return ESP_OK;
}

esp_err_t host_comm_deinit(host_comm_t *comm) {
    if (!host_comm_have_handle(comm)) {
        return ESP_ERR_INVALID_STATE;
    }

    // Tear the handle down even if the transport driver complains: bailing out
    // early used to leave the mutex live, and the next host_comm_init()
    // overwrote comm->mutex, leaking one semaphore per attempt.
    esp_err_t ret = transport_deinit(&comm->transport);
    if (ret != ESP_OK) {
        ESP_LOGE(TAG, "Failed to deinitialize transport: %s", esp_err_to_name(ret));
    }

    vSemaphoreDelete(comm->mutex);
    comm->mutex = NULL;

    comm->link_up = false;
    ESP_LOGI(TAG, "Host communication deinitialized");

    return ret;
}

const char* host_comm_get_transport_name(host_comm_t *comm) {
    if (!host_comm_have_handle(comm)) {
        return "Not initialized";
    }
    return transport_get_name(&comm->transport);
}

// Helper function to poll for async operation completion and retrieve result
static esp_err_t host_comm_poll_async_result(host_comm_t *comm, uint32_t timeout_ms, uint32_t poll_interval_ms,
                                             size_t expected_size, uint8_t **result_data, size_t *actual_size) {
    if (!host_comm_have_handle(comm)) {
        return ESP_ERR_INVALID_ARG;
    }

    uint32_t elapsed_ms = 0;
    bool ready = false;
    uint16_t response_size = 0;

    // Immediate poll before delay loop (reduces latency for fast async ops at 20MHz)
    esp_err_t ret = transport_poll_async_status(&comm->transport, &ready, &response_size,
                                                rx_buffer, expected_size);
    if (ret != ESP_OK) {
        return ret;
    }

    while (elapsed_ms < timeout_ms && !ready) {
        vTaskDelay(pdMS_TO_TICKS(poll_interval_ms));
        elapsed_ms += poll_interval_ms;

        ret = transport_poll_async_status(&comm->transport, &ready, &response_size,
                                                    rx_buffer, expected_size);
        if (ret != ESP_OK) {
            return ret;
        }
    }

    if (!ready) {
        ESP_LOGE(TAG, "Async operation timeout after %u ms", elapsed_ms);
        return ESP_ERR_TIMEOUT;
    }

    if (expected_size > 0 && response_size > expected_size) {
        ESP_LOGE(TAG, "Response too large: %u (max %u)", response_size, expected_size);
        return ESP_ERR_INVALID_RESPONSE;
    }

    if (result_data) {
        *result_data = rx_buffer;
    }
    if (actual_size) {
        *actual_size = response_size;
    }

    return ESP_OK;
}


// Directory browsing functions

esp_err_t host_comm_get_entry_count(host_comm_t *comm, uint16_t device_index, uint32_t *count) {
    if (!host_comm_have_handle(comm) || !count) {
        return ESP_ERR_INVALID_ARG;
    }

    HOST_COMM_LOCK(comm);

    // Start the entry count operation
    esp_err_t ret = transport_two_phase_transaction(&comm->transport,
                                                    PANEL_CMD_GET_DIR_ENTRY_COUNT, device_index,
                                                    NULL, 0,  // No write data
                                                    NULL, 0);  // No read data
    if (ret != ESP_OK) {
        HOST_COMM_UNLOCK(comm);
        return ret;
    }

    // Poll for completion with 1 second timeout
    uint8_t *result_data;
    size_t result_size;
    ret = host_comm_poll_async_result(comm, 1000, 10, 4, &result_data, &result_size);
    if (ret != ESP_OK) {
        HOST_COMM_UNLOCK(comm);
        return ret;
    }

    // Parse the 4-byte big-endian entry count
    *count = (result_data[0] << 24) | (result_data[1] << 16) | (result_data[2] << 8) | result_data[3];
    ESP_LOGI(TAG, "Entry count: %lu", *count);

    HOST_COMM_UNLOCK(comm);
    return ESP_OK;
}

esp_err_t host_comm_get_entry_info(host_comm_t *comm, uint16_t device_index, uint32_t index,
                                   dir_entry_info_t *info) {
    if (!host_comm_have_handle(comm) || !info) {
        return ESP_ERR_INVALID_ARG;
    }

    HOST_COMM_LOCK(comm);

    ESP_LOGI(TAG, "Getting info for entry: %lu", index);

    // Only allow up to 65535 entries
    if (index >= PANEL_ARG_EXTENDED) {
        HOST_COMM_UNLOCK(comm);
        return ESP_ERR_INVALID_ARG;
    }
    tx_buffer[0] = (uint8_t)device_index;

    esp_err_t ret = transport_two_phase_transaction(&comm->transport,
                                                    PANEL_CMD_GET_ENTRY_INFO, (uint16_t)index,
                                                    tx_buffer, 1,  // device only
                                                    NULL, 0);  // No read data

    if (ret != ESP_OK) {
        HOST_COMM_UNLOCK(comm);
        return ret;
    }

    // Poll for completion with 1 second timeout
    uint8_t *result_data;
    size_t result_size;
    ret = host_comm_poll_async_result(comm, 1000, 10, sizeof(dir_entry_info_t), &result_data, &result_size);
    if (ret != ESP_OK) {
        HOST_COMM_UNLOCK(comm);
        return ret;
    }

    // Copy result to caller's buffer
    memcpy(info, result_data, sizeof(dir_entry_info_t));
    ESP_LOGI(TAG, "Got entry info: %s (type=%u)", info->name, info->entry_type);

    HOST_COMM_UNLOCK(comm);
    return ret;
}

esp_err_t host_comm_select_entry(host_comm_t *comm, int32_t index, uint16_t device_index) {
    if (!host_comm_have_handle(comm)) {
        return ESP_ERR_INVALID_ARG;
    }

    HOST_COMM_LOCK(comm);

    ESP_LOGI(TAG, "Selecting entry: %ld (device %u)", index, device_index);

    // Send command with signed 16-bit index in argument field
    int16_t index16 = (int16_t)index;

    // Send device_index as 1-byte payload so BlueSCSI targets the correct device
    uint8_t payload[1] = { (uint8_t)device_index };
    esp_err_t ret = transport_two_phase_transaction(&comm->transport,
                                                    PANEL_CMD_SELECT_ENTRY, (uint16_t)index16,
                                                    payload, sizeof(payload),
                                                    NULL, 0);  // No read data
    if (ret != ESP_OK) {
        HOST_COMM_UNLOCK(comm);
        return ret;
    }

    // Poll for completion with 2 second timeout (may need to load image)
    // BlueSCSI returns 1-byte result code that must be read to clear SPI state
    ret = host_comm_poll_async_result(comm, 2000, 10, 1, NULL, NULL);
    HOST_COMM_UNLOCK(comm);
    return ret;
}

esp_err_t host_comm_get_current_path(host_comm_t *comm, uint16_t device_index, char *path, size_t max_len) {
    if (!host_comm_have_handle(comm) || !path || max_len == 0) {
        return ESP_ERR_INVALID_ARG;
    }

    HOST_COMM_LOCK(comm);

    ESP_LOGI(TAG, "Getting current path");

    // Start the get path operation
    esp_err_t ret = transport_two_phase_transaction(&comm->transport,
                                                    PANEL_CMD_GET_CURRENT_PATH, device_index,
                                                    NULL, 0,  // No write data
                                                    NULL, 0);  // No read data
    if (ret != ESP_OK) {
        HOST_COMM_UNLOCK(comm);
        return ret;
    }

    // Poll for completion with 1 second timeout
    // Path response is fixed 128 bytes with null-terminated string inside
    uint8_t *result_data;
    size_t result_size;
    ret = host_comm_poll_async_result(comm, 1000, 10, 128, &result_data, &result_size);
    if (ret != ESP_OK) {
        HOST_COMM_UNLOCK(comm);
        return ret;
    }

    // Copy path string to caller's buffer
    size_t copy_len = (result_size < max_len) ? result_size : (max_len - 1);
    memcpy(path, result_data, copy_len);
    path[copy_len] = '\0';

    ESP_LOGI(TAG, "Current path: %s", path);

    HOST_COMM_UNLOCK(comm);
    return ESP_OK;
}

// Image management functions

esp_err_t host_comm_select_prev_image(host_comm_t *comm, uint16_t device_index) {
    if (!host_comm_have_handle(comm)) {
        return ESP_ERR_INVALID_ARG;
    }

    HOST_COMM_LOCK(comm);

    ESP_LOGI(TAG, "Selecting previous image (device %u)", device_index);

    esp_err_t ret = transport_two_phase_transaction(&comm->transport,
                                                    PANEL_CMD_SELECT_PREV_IMAGE, device_index,
                                                    NULL, 0,  // No write data
                                                    NULL, 0);  // No read data
    if (ret != ESP_OK) {
        HOST_COMM_UNLOCK(comm);
        return ret;
    }

    // Poll for completion
    ret = host_comm_poll_async_result(comm, 2000, 10, 0, NULL, NULL);
    HOST_COMM_UNLOCK(comm);
    return ret;
}

esp_err_t host_comm_select_next_image(host_comm_t *comm, uint16_t device_index) {
    if (!host_comm_have_handle(comm)) {
        return ESP_ERR_INVALID_ARG;
    }

    HOST_COMM_LOCK(comm);

    ESP_LOGI(TAG, "Selecting next image (device %u)", device_index);

    esp_err_t ret = transport_two_phase_transaction(&comm->transport,
                                                    PANEL_CMD_SELECT_NEXT_IMAGE, device_index,
                                                    NULL, 0,  // No write data
                                                    NULL, 0);  // No read data
    if (ret != ESP_OK) {
        HOST_COMM_UNLOCK(comm);
        return ret;
    }

    // Poll for completion
    ret = host_comm_poll_async_result(comm, 2000, 10, 0, NULL, NULL);
    HOST_COMM_UNLOCK(comm);
    return ret;
}

esp_err_t host_comm_eject_image(host_comm_t *comm, uint16_t device_index) {
    if (!host_comm_have_handle(comm)) {
        return ESP_ERR_INVALID_ARG;
    }

    HOST_COMM_LOCK(comm);

    ESP_LOGI(TAG, "Ejecting image (device %u)", device_index);

    esp_err_t ret = transport_two_phase_transaction(&comm->transport,
                                                    PANEL_CMD_EJECT_IMAGE, device_index,
                                                    NULL, 0,  // No write data
                                                    NULL, 0);  // No read data
    if (ret != ESP_OK) {
        HOST_COMM_UNLOCK(comm);
        return ret;
    }

    // Poll for completion
    ret = host_comm_poll_async_result(comm, 1000, 10, 0, NULL, NULL);
    HOST_COMM_UNLOCK(comm);
    return ret;
}

esp_err_t host_comm_get_loaded_image_status(host_comm_t *comm, uint16_t device_index, loaded_image_status_t *status) {
    if (!host_comm_have_handle(comm) || !status) {
        return ESP_ERR_INVALID_ARG;
    }

    HOST_COMM_LOCK(comm);

    ESP_LOGI(TAG, "Getting loaded image status (device %u)", device_index);

    // Start the get status operation
    esp_err_t ret = transport_two_phase_transaction(&comm->transport,
                                                    PANEL_CMD_GET_LOADED_IMAGE_STATUS, device_index,
                                                    NULL, 0,  // No write data
                                                    NULL, 0);  // No read data
    if (ret != ESP_OK) {
        HOST_COMM_UNLOCK(comm);
        return ret;
    }

    // Poll for completion with 1 second timeout
    uint8_t *result_data;
    size_t result_size;
    ret = host_comm_poll_async_result(comm, 1000, 10, sizeof(loaded_image_status_t), &result_data, &result_size);
    if (ret != ESP_OK) {
        HOST_COMM_UNLOCK(comm);
        return ret;
    }

    // Copy result to caller's buffer
    memcpy(status, result_data, sizeof(loaded_image_status_t));
    ESP_LOGI(TAG, "Image status: loaded=%u, name=%s", status->image_loaded, status->image_name);

    HOST_COMM_UNLOCK(comm);
    return ret;
}

// Status functions

esp_err_t host_comm_get_device_status(host_comm_t *comm, uint16_t device_index, uint8_t *status) {
    if (!host_comm_have_handle(comm) || !status) {
        return ESP_ERR_INVALID_ARG;
    }

    HOST_COMM_LOCK(comm);

    ESP_LOGI(TAG, "Getting device status (device %u)", device_index);

    uint8_t device_status;
    esp_err_t ret = transport_two_phase_transaction(&comm->transport,
                                                    PANEL_CMD_GET_DEVICE_STATUS, device_index,
                                                    NULL, 0,  // No write data
                                                    &device_status, 1);  // Read 1 byte
    if (ret == ESP_OK) {
        *status = device_status;
    }

    HOST_COMM_UNLOCK(comm);
    return ret;
}

esp_err_t host_comm_get_playback_status(host_comm_t *comm, uint16_t device_index, playback_status_t *status) {
    if (!host_comm_have_handle(comm) || !status) {
        return ESP_ERR_INVALID_ARG;
    }

    HOST_COMM_LOCK(comm);

    ESP_LOGD(TAG, "Getting playback status (device %u)", device_index);

    esp_err_t ret = transport_two_phase_transaction(&comm->transport,
                                                    PANEL_CMD_GET_PLAYBACK_STATUS, device_index,
                                                    NULL, 0,
                                                    (uint8_t*)status, sizeof(playback_status_t));
    if (ret == ESP_OK) {
        ESP_LOGD(TAG, "Playback status: flags=0x%02x, type=%d, track=%d",
                status->flags, status->disc_type, status->current_track);
    }

    HOST_COMM_UNLOCK(comm);
    return ret;
}

#ifdef CONFIG_PRODUCT_BLUESCSI
esp_err_t host_comm_get_initiator_summary(host_comm_t *comm,
                                          panel_initiator_summary_t *summary) {
    if (!host_comm_have_handle(comm) || !summary) {
        return ESP_ERR_INVALID_ARG;
    }

    HOST_COMM_LOCK(comm);

    esp_err_t ret = transport_two_phase_transaction(&comm->transport,
                                                    PANEL_CMD_GET_INITIATOR_SUMMARY,
                                                    PANEL_ARG_IGNORED,
                                                    NULL, 0,
                                                    (uint8_t*)summary,
                                                    sizeof(panel_initiator_summary_t));

    HOST_COMM_UNLOCK(comm);

    if (ret != ESP_OK) {
        return ret;
    }
    // Same guard as the playback status: an absent board reads back as a
    // uniform 0x00/0xFF bus, which would otherwise look like a valid summary.
    if (summary->alive_magic != PANEL_ALIVE_MAGIC) {
        return ESP_ERR_INVALID_RESPONSE;
    }
    return ESP_OK;
}
#endif

esp_err_t host_comm_probe_alive(host_comm_t *comm, uint16_t device_index) {
    playback_status_t status;
    esp_err_t ret = host_comm_get_playback_status(comm, device_index, &status);
    if (ret != ESP_OK) {
        return ret;
    }
    // A transaction that "succeeds" is not proof of a live host: SPI reads
    // from an absent host return ESP_OK with whatever the floating MISO line
    // clocked in. Only the alive magic confirms a main board answered.
    if (status.alive_magic != PANEL_ALIVE_MAGIC) {
        return ESP_ERR_INVALID_RESPONSE;
    }

    // The magic alone is one byte at a fixed offset, and repeating the read is
    // NOT an independent sample — a floating input settles to a level set by
    // leakage and coupling, so a bus that clocks in a uniform 0xA5 reproduces it
    // every time. Reject a response whose bytes are all identical, which is the
    // shape undriven and stuck-bus reads actually take. A live board never
    // matches: its boolean fields cannot all equal 0xA5.
    const uint8_t *raw = (const uint8_t *)&status;
    bool uniform = true;
    for (size_t i = 1; i < sizeof(status); i++) {
        if (raw[i] != raw[0]) {
            uniform = false;
            break;
        }
    }
    if (uniform) {
        return ESP_ERR_INVALID_RESPONSE;
    }

    // Cross-check a second, independently-constrained field: only defined flag
    // bits are ever set, so anything else means we are reading noise.
    if (status.flags & ~PANEL_PB_FLAGS_KNOWN) {
        return ESP_ERR_INVALID_RESPONSE;
    }

    return ESP_OK;
}

esp_err_t host_comm_check_firmware(host_comm_t *comm, panel_firmware_info_t *info) {
    if (!host_comm_have_handle(comm) || !info) {
        return ESP_ERR_INVALID_ARG;
    }

    HOST_COMM_LOCK(comm);

    ESP_LOGI(TAG, "Checking for firmware updates...");

    // Send CHECK_FIRMWARE command (async operation)
    esp_err_t ret = transport_two_phase_transaction(&comm->transport,
                                           PANEL_CMD_CHECK_FIRMWARE, PANEL_ARG_IGNORED,
                                           NULL, 0,  // No write data
                                           NULL, 0); // No immediate read data
    if (ret != ESP_OK) {
        ESP_LOGE(TAG, "Failed to send firmware check command: %s", esp_err_to_name(ret));
        HOST_COMM_UNLOCK(comm);
        return ret;
    }

    // Poll for async result - keep mutex held to prevent other commands
    // from interfering with the async state
    uint8_t *result_data;
    size_t result_size;
    ret = host_comm_poll_async_result(comm, 5000, 10, sizeof(panel_firmware_info_t), &result_data, &result_size);
    if (ret != ESP_OK) {
        ESP_LOGE(TAG, "Failed to get firmware check result: %s", esp_err_to_name(ret));
        HOST_COMM_UNLOCK(comm);
        return ret;
    }

    // Copy result to caller's buffer
    memcpy(info, result_data, sizeof(panel_firmware_info_t));

    char sha256_hex[65];
    for (int i = 0; i < 32; i++) {
        snprintf(sha256_hex + (i * 2), sizeof(sha256_hex) - (i * 2), "%02x", info->sha256[i]);
    }
    ESP_LOGI(TAG, "Firmware info - Available: %d, Size: %lu, Version: 0x%08lx, SHA256: %s",
             info->available, info->size, info->version, sha256_hex);

    HOST_COMM_UNLOCK(comm);
    return ESP_OK;
}

esp_err_t host_comm_read_firmware_chunk(host_comm_t *comm, uint32_t offset,
                                        uint8_t *buffer, size_t size) {
    if (!host_comm_have_handle(comm) || !buffer || size == 0) {
        return ESP_ERR_INVALID_ARG;
    }

    if (size > PANEL_FIRMWARE_CHUNK_SIZE) {
        ESP_LOGE(TAG, "Chunk size too large: %d > %d", size, PANEL_FIRMWARE_CHUNK_SIZE);
        return ESP_ERR_INVALID_SIZE;
    }

    HOST_COMM_LOCK(comm);

    ESP_LOGD(TAG, "Reading firmware chunk at offset 0x%lx, size %d", offset, size);

    // Prepare offset in tx_buffer (little endian)
    tx_buffer[0] = offset & 0xFF;
    tx_buffer[1] = (offset >> 8) & 0xFF;
    tx_buffer[2] = (offset >> 16) & 0xFF;
    tx_buffer[3] = (offset >> 24) & 0xFF;

    // Send START_FIRMWARE_READ command with offset
    esp_err_t ret = transport_two_phase_transaction(&comm->transport,
                                                    PANEL_CMD_START_FIRMWARE_READ, PANEL_ARG_EXTENDED,
                                                    tx_buffer, 4,  // Send offset
                                                    NULL, 0);      // No immediate read data
    if (ret != ESP_OK) {
        ESP_LOGE(TAG, "Failed to send firmware read command: %s", esp_err_to_name(ret));
        HOST_COMM_UNLOCK(comm);
        return ret;
    }

    // Wait for chunk to be ready and read it
    uint8_t *result_data;
    size_t result_size;
    ret = host_comm_poll_async_result(comm, 5000, 10, size, &result_data, &result_size);
    if (ret != ESP_OK) {
        ESP_LOGE(TAG, "Failed to get firmware chunk: %s", esp_err_to_name(ret));
        HOST_COMM_UNLOCK(comm);
        return ret;
    }

    if (result_size != size) {
        ESP_LOGE(TAG, "Firmware chunk size mismatch: expected %d, got %d", size, result_size);
        HOST_COMM_UNLOCK(comm);
        return ESP_ERR_INVALID_SIZE;
    }

    // Copy chunk data to caller's buffer
    memcpy(buffer, result_data, size);

    ESP_LOGD(TAG, "Successfully read firmware chunk: %d bytes", size);
    HOST_COMM_UNLOCK(comm);
    return ESP_OK;
}

esp_err_t host_comm_start_file_upload(host_comm_t *comm, const char *filename, uint32_t file_size) {
    if (!host_comm_have_handle(comm) || !filename) {
        return ESP_ERR_INVALID_ARG;
    }

    // Validate filename length before locking
    size_t filename_len = strlen(filename);
    if (filename_len > (PANEL_PROTOCOL_MAX_PAYLOAD - sizeof(panel_file_upload_start_t) - 1)) {
        ESP_LOGE(TAG, "Filename too long: %d bytes", filename_len);
        return ESP_ERR_INVALID_ARG;
    }

    HOST_COMM_LOCK(comm);

    ESP_LOGI(TAG, "Starting file upload: %s (%u bytes)", filename, file_size);

    // Prepare payload with file upload start structure
    panel_file_upload_start_t *upload_start = (panel_file_upload_start_t *)tx_buffer;
    upload_start->file_size = file_size;
    upload_start->filename_len = filename_len;

    // Copy filename after the structure (null-terminated)
    memcpy(tx_buffer + sizeof(panel_file_upload_start_t), filename, filename_len);
    tx_buffer[sizeof(panel_file_upload_start_t) + filename_len] = '\0';

    size_t total_payload_size = sizeof(panel_file_upload_start_t) + filename_len + 1;

    // Send START_FILE_UPLOAD command (async operation)
    esp_err_t ret = transport_two_phase_transaction(&comm->transport,
                                                   PANEL_CMD_START_FILE_UPLOAD, PANEL_ARG_EXTENDED,
                                                   tx_buffer, total_payload_size,
                                                   NULL, 0); // No immediate read data

    if (ret != ESP_OK) {
        ESP_LOGE(TAG, "Failed to start file upload: %s", esp_err_to_name(ret));
        HOST_COMM_UNLOCK(comm);
        return ret;
    }

    // Poll for async result (mirrors START_FILE_DOWNLOAD's timeout)
    ret = host_comm_poll_async_result(comm, 5000, 10, 0, NULL, NULL);
    if (ret != ESP_OK) {
        ESP_LOGE(TAG, "Failed async result after start upload: %s", esp_err_to_name(ret));
        HOST_COMM_UNLOCK(comm);
        return ret;
    }

    ESP_LOGD(TAG, "File upload start command sent successfully");
    HOST_COMM_UNLOCK(comm);
    return ESP_OK;
}

esp_err_t host_comm_write_file_chunk(host_comm_t *comm, const uint8_t *data, size_t size) {
    if (!host_comm_have_handle(comm) || !data || size == 0) {
        return ESP_ERR_INVALID_ARG;
    }

    if (size > PANEL_FILE_CHUNK_SIZE) {
        ESP_LOGE(TAG, "Chunk size too large: %d bytes (max %d)", size, PANEL_FILE_CHUNK_SIZE);
        return ESP_ERR_INVALID_ARG;
    }

    HOST_COMM_LOCK(comm);

    /* ESP_LOGD(TAG, "Writing file chunk: %d bytes", size); */

    // Copy chunk data to tx buffer
    memcpy(tx_buffer, data, size);

    // Calc CRC16 of chunk
    uint16_t chunk_crc16 = ~esp_rom_crc16_be((uint16_t)~0xffff, data, size);

    // Send WRITE_FILE_CHUNK command (async operation)
    esp_err_t ret = transport_two_phase_transaction(&comm->transport,
                                                   PANEL_CMD_WRITE_FILE_CHUNK, chunk_crc16,
                                                   tx_buffer, size,
                                                   NULL, 0); // No immediate read data

    if (ret != ESP_OK) {
        ESP_LOGE(TAG, "Failed to write file chunk: %s", esp_err_to_name(ret));
        HOST_COMM_UNLOCK(comm);
        return ret;
    }

    // Poll for async result
    ret = host_comm_poll_async_result(comm, 5000, 10, 0, NULL, NULL);

    if (ret != ESP_OK) {
        ESP_LOGE(TAG, "Failed async result after write: %s", esp_err_to_name(ret));
        HOST_COMM_UNLOCK(comm);
        return ret;
    }

    /* ESP_LOGD(TAG, "File chunk written successfully"); */
    HOST_COMM_UNLOCK(comm);
    return ESP_OK;
}

esp_err_t host_comm_finish_file_upload(host_comm_t *comm, uint8_t *result_code, uint8_t *file_hash) {
    if (!host_comm_have_handle(comm)) {
        return ESP_ERR_INVALID_ARG;
    }

    HOST_COMM_LOCK(comm);

    ESP_LOGI(TAG, "Finishing file upload");

    // Send FINISH_FILE_UPLOAD command (async operation)
    esp_err_t ret = transport_two_phase_transaction(&comm->transport,
                                                   PANEL_CMD_FINISH_FILE_UPLOAD, PANEL_ARG_IGNORED,
                                                   NULL, 0,  // No write data
                                                   NULL, 0); // No immediate read data

    if (ret != ESP_OK) {
        ESP_LOGE(TAG, "Failed to send finish file upload command: %s", esp_err_to_name(ret));
        HOST_COMM_UNLOCK(comm);
        return ret;
    }

    // Poll for async result (33 bytes: 1 byte result code + 32 byte SHA256).
    // Generous timeout: finish flushes/closes the file and finalizes the SHA.
    uint8_t *result_data;
    size_t result_size;
    ret = host_comm_poll_async_result(comm, 30000, 10, 33, &result_data, &result_size);
    if (ret != ESP_OK) {
        ESP_LOGE(TAG, "Failed to get file upload result: %s", esp_err_to_name(ret));
        HOST_COMM_UNLOCK(comm);
        return ret;
    }

    if (result_size != 33) {
        ESP_LOGE(TAG, "Upload result size mismatch: expected 33, got %d", result_size);
        HOST_COMM_UNLOCK(comm);
        return ESP_ERR_INVALID_SIZE;
    }

    if (result_code) {
        *result_code = result_data[0];
    }

    // Copy SHA256 hash if buffer provided
    if (file_hash) {
        memcpy(file_hash, result_data + 1, 32);
    }

    if (result_data[0] == PANEL_UPLOAD_OK) {
        // Log the hash in hex format
        char hash_hex[65];
        for (int i = 0; i < 32; i++) {
            snprintf(hash_hex + (i * 2), sizeof(hash_hex) - (i * 2), "%02x", result_data[1 + i]);
        }
        ESP_LOGI(TAG, "File upload completed successfully. SHA256: %s", hash_hex);
    } else {
        ESP_LOGE(TAG, "File upload failed with code: 0x%02X", result_data[0]);
    }

    HOST_COMM_UNLOCK(comm);
    return ESP_OK;
}

esp_err_t host_comm_start_file_download(host_comm_t *comm, const char *filename, uint32_t *file_size) {
    if (!host_comm_have_handle(comm) || !filename || !file_size) {
        return ESP_ERR_INVALID_ARG;
    }

    // Validate filename length before locking
    size_t filename_len = strlen(filename);
    if (filename_len >= PANEL_PROTOCOL_MAX_PAYLOAD) {
        ESP_LOGE(TAG, "Filename too long: %d bytes", filename_len);
        return ESP_ERR_INVALID_ARG;
    }

    HOST_COMM_LOCK(comm);

    ESP_LOGI(TAG, "Starting file download: %s", filename);

    // Prepare payload with filename (null-terminated)
    memcpy(tx_buffer, filename, filename_len);
    tx_buffer[filename_len] = '\0';

    // Send START_FILE_DOWNLOAD command (async operation)
    esp_err_t ret = transport_two_phase_transaction(&comm->transport,
                                                   PANEL_CMD_START_FILE_DOWNLOAD, PANEL_ARG_EXTENDED,
                                                   tx_buffer, filename_len + 1,
                                                   NULL, 0);

    if (ret != ESP_OK) {
        ESP_LOGE(TAG, "Failed to start file download: %s", esp_err_to_name(ret));
        HOST_COMM_UNLOCK(comm);
        return ret;
    }

    // Poll for async result (5 bytes: panel_file_download_start_result_t)
    uint8_t *result_data;
    size_t result_size;
    ret = host_comm_poll_async_result(comm, 5000, 10, sizeof(panel_file_download_start_result_t),
                                      &result_data, &result_size);
    if (ret != ESP_OK) {
        ESP_LOGE(TAG, "Failed to get file download start result: %s", esp_err_to_name(ret));
        HOST_COMM_UNLOCK(comm);
        return ret;
    }

    if (result_size < sizeof(panel_file_download_start_result_t)) {
        ESP_LOGE(TAG, "Download result size mismatch: expected %d, got %d",
                 sizeof(panel_file_download_start_result_t), result_size);
        HOST_COMM_UNLOCK(comm);
        return ESP_ERR_INVALID_SIZE;
    }

    panel_file_download_start_result_t *result = (panel_file_download_start_result_t *)result_data;

    if (result->result_code != PANEL_DOWNLOAD_OK) {
        ESP_LOGE(TAG, "File download start failed with code: 0x%02X", result->result_code);
        HOST_COMM_UNLOCK(comm);
        return ESP_ERR_NOT_FOUND;
    }

    *file_size = result->file_size;
    ESP_LOGI(TAG, "File download started: %lu bytes", result->file_size);
    HOST_COMM_UNLOCK(comm);
    return ESP_OK;
}

esp_err_t host_comm_read_file_chunk(host_comm_t *comm, uint32_t chunk_index, uint8_t *buffer, size_t *bytes_read) {
    if (!host_comm_have_handle(comm) || !buffer || !bytes_read) {
        return ESP_ERR_INVALID_ARG;
    }

    HOST_COMM_LOCK(comm);

    // Store chunk index in tx buffer
    memcpy(tx_buffer, &chunk_index, sizeof(chunk_index));

    // Send READ_FILE_CHUNK command (async operation)
    esp_err_t ret = transport_two_phase_transaction(&comm->transport,
                                                   PANEL_CMD_READ_FILE_CHUNK, chunk_index,
                                                   tx_buffer, sizeof(chunk_index),
                                                   NULL, 0);

    if (ret != ESP_OK) {
        ESP_LOGE(TAG, "Failed to send read file chunk command: %s", esp_err_to_name(ret));
        HOST_COMM_UNLOCK(comm);
        return ret;
    }

    // Poll for async result (size varies - could be less than chunk size for last/small files)
    // Pass max chunk size so the data actually gets read from SPI
    uint8_t *result_data;
    size_t result_size;
    ret = host_comm_poll_async_result(comm, 5000, 10, PANEL_FILE_CHUNK_SIZE, &result_data, &result_size);
    if (ret != ESP_OK) {
        ESP_LOGE(TAG, "Failed to get file chunk: %s", esp_err_to_name(ret));
        HOST_COMM_UNLOCK(comm);
        return ret;
    }

    memcpy(buffer, result_data, result_size);
    *bytes_read = result_size;

    ESP_LOGD(TAG, "File chunk read: index=%lu, size=%d", chunk_index, result_size);
    HOST_COMM_UNLOCK(comm);
    return ESP_OK;
}

// Shared helper: send one (path2 == NULL) or two null-terminated path strings
// with `command` and read back a 1-byte result code. Used by delete, rename,
// touch and mkdir.
static esp_err_t host_comm_path_op(host_comm_t *comm, uint8_t command,
                                   const char *path, const char *path2,
                                   uint8_t *result_code) {
    if (!host_comm_have_handle(comm) || !path || !result_code) {
        return ESP_ERR_INVALID_ARG;
    }

    size_t path_len = strlen(path);
    size_t path2_len = path2 ? strlen(path2) : 0;
    size_t payload_size = path_len + 1 + (path2 ? path2_len + 1 : 0);
    if (path_len == 0 || (path2 && path2_len == 0) ||
        payload_size > PANEL_PROTOCOL_MAX_PAYLOAD) {
        ESP_LOGE(TAG, "Path op 0x%02X path lengths invalid: %d / %d bytes",
                 command, path_len, path2_len);
        return ESP_ERR_INVALID_ARG;
    }

    HOST_COMM_LOCK(comm);

    // Payload: path\0[path2\0]
    memcpy(tx_buffer, path, path_len);
    tx_buffer[path_len] = '\0';
    if (path2) {
        memcpy(tx_buffer + path_len + 1, path2, path2_len);
        tx_buffer[path_len + 1 + path2_len] = '\0';
    }

    esp_err_t ret = transport_two_phase_transaction(&comm->transport,
                                                   command, PANEL_ARG_EXTENDED,
                                                   tx_buffer, payload_size,
                                                   NULL, 0);
    if (ret != ESP_OK) {
        ESP_LOGE(TAG, "Failed to send path op 0x%02X: %s", command, esp_err_to_name(ret));
        HOST_COMM_UNLOCK(comm);
        return ret;
    }

    uint8_t *result_data;
    size_t result_size;
    ret = host_comm_poll_async_result(comm, 5000, 10, 1, &result_data, &result_size);
    if (ret != ESP_OK) {
        ESP_LOGE(TAG, "Failed to get path-op result: %s", esp_err_to_name(ret));
        HOST_COMM_UNLOCK(comm);
        return ret;
    }

    if (result_size < 1) {
        ESP_LOGE(TAG, "Path-op result size mismatch: got %d", result_size);
        HOST_COMM_UNLOCK(comm);
        return ESP_ERR_INVALID_SIZE;
    }

    *result_code = result_data[0];
    ESP_LOGD(TAG, "Path op 0x%02X result code: 0x%02X", command, *result_code);
    HOST_COMM_UNLOCK(comm);
    return ESP_OK;
}

esp_err_t host_comm_delete_file(host_comm_t *comm, const char *path, uint8_t *result_code) {
    ESP_LOGI(TAG, "Deleting file: %s", path ? path : "(null)");
    return host_comm_path_op(comm, PANEL_CMD_DELETE_FILE, path, NULL, result_code);
}

esp_err_t host_comm_rename_file(host_comm_t *comm, const char *old_path,
                                const char *new_path, uint8_t *result_code) {
    if (!new_path) {
        return ESP_ERR_INVALID_ARG;
    }
    ESP_LOGI(TAG, "Renaming file: %s -> %s", old_path ? old_path : "(null)", new_path);
    return host_comm_path_op(comm, PANEL_CMD_RENAME_FILE, old_path, new_path, result_code);
}

esp_err_t host_comm_touch_file(host_comm_t *comm, const char *path, uint8_t *result_code) {
    ESP_LOGI(TAG, "Touching file: %s", path ? path : "(null)");
    return host_comm_path_op(comm, PANEL_CMD_TOUCH_FILE, path, NULL, result_code);
}

esp_err_t host_comm_mkdir(host_comm_t *comm, const char *path, uint8_t *result_code) {
    ESP_LOGI(TAG, "Creating directory: %s", path ? path : "(null)");
    return host_comm_path_op(comm, PANEL_CMD_MKDIR, path, NULL, result_code);
}

esp_err_t host_comm_get_rp2350_fw_status(host_comm_t *comm, rp2350_fw_status_t *status) {
    if (!host_comm_have_handle(comm) || !status) {
        return ESP_ERR_INVALID_ARG;
    }

    HOST_COMM_LOCK(comm);

    ESP_LOGI(TAG, "Getting RP2350 firmware status...");

    // Send GET_RP2350_FW_STATUS command (async operation)
    esp_err_t ret = transport_two_phase_transaction(&comm->transport,
                                                    PANEL_CMD_GET_RP2350_FW_STATUS, PANEL_ARG_IGNORED,
                                                    NULL, 0,  // No write data
                                                    NULL, 0); // No immediate read data
    if (ret != ESP_OK) {
        ESP_LOGE(TAG, "Failed to send RP2350 fw status command: %s", esp_err_to_name(ret));
        HOST_COMM_UNLOCK(comm);
        return ret;
    }

    // Poll for async result
    uint8_t *result_data;
    size_t result_size;
    ret = host_comm_poll_async_result(comm, 2000, 10, sizeof(rp2350_fw_status_t), &result_data, &result_size);
    if (ret != ESP_OK) {
        ESP_LOGE(TAG, "Failed to get RP2350 fw status result: %s", esp_err_to_name(ret));
        HOST_COMM_UNLOCK(comm);
        return ret;
    }

    // Copy result to caller's buffer
    memcpy(status, result_data, sizeof(rp2350_fw_status_t));

    ESP_LOGI(TAG, "RP2350 status: version=0x%08lx, avail=0x%08lx",
             status->current_version, status->available_version);

    HOST_COMM_UNLOCK(comm);
    return ESP_OK;
}

esp_err_t host_comm_start_rp2350_update(host_comm_t *comm) {
    if (!host_comm_have_handle(comm)) {
        return ESP_ERR_INVALID_STATE;
    }

    HOST_COMM_LOCK(comm);

    ESP_LOGI(TAG, "Starting RP2350 firmware update...");

    // Send START_RP2350_UPDATE command (async operation)
    // The main board will start updating and reboot when done - don't wait for response
    esp_err_t ret = transport_two_phase_transaction(&comm->transport,
                                                    PANEL_CMD_START_RP2350_UPDATE, PANEL_ARG_IGNORED,
                                                    NULL, 0,  // No write data
                                                    NULL, 0); // No immediate read data
    if (ret != ESP_OK) {
        ESP_LOGE(TAG, "Failed to send RP2350 update command: %s", esp_err_to_name(ret));
        HOST_COMM_UNLOCK(comm);
        return ret;
    }

    // Don't poll - the update happens quickly and the board reboots
    // The caller should detect the reboot and wait for the board to come back
    ESP_LOGI(TAG, "RP2350 update command sent successfully");
    HOST_COMM_UNLOCK(comm);
    return ESP_OK;
}

esp_err_t host_comm_get_device_list(host_comm_t *comm, device_list_response_t *response, size_t max_size) {
    if (!host_comm_have_handle(comm) || !response || max_size < sizeof(device_list_response_t)) {
        return ESP_ERR_INVALID_ARG;
    }

    HOST_COMM_LOCK(comm);

    ESP_LOGI(TAG, "Getting device list");

    // Start the get device list operation
    esp_err_t ret = transport_two_phase_transaction(&comm->transport,
                                                    PANEL_CMD_GET_DEVICE_LIST, PANEL_ARG_IGNORED,
                                                    NULL, 0,  // No write data
                                                    NULL, 0);  // No read data
    if (ret != ESP_OK) {
        HOST_COMM_UNLOCK(comm);
        return ret;
    }

    // Poll for completion with 2 second timeout
    uint8_t *result_data;
    size_t result_size;
    ret = host_comm_poll_async_result(comm, 2000, 10, max_size, &result_data, &result_size);
    if (ret != ESP_OK) {
        HOST_COMM_UNLOCK(comm);
        return ret;
    }

    // Copy result to caller's buffer
    size_t copy_size = (result_size < max_size) ? result_size : max_size;
    memcpy(response, result_data, copy_size);

    // Callers iterate devices[] up to device_count. A truncated or garbled reply
    // would walk off the end, so clamp the count to what actually arrived.
    size_t capacity = (copy_size > sizeof(device_list_response_t))
        ? (copy_size - sizeof(device_list_response_t)) / sizeof(device_summary_t) : 0;
    if (response->device_count > capacity) {
        ESP_LOGW(TAG, "Device list truncated: %u of %u devices fit",
                 (unsigned)capacity, response->device_count);
        response->device_count = (uint8_t)capacity;
    }

    ESP_LOGI(TAG, "Device list: %u devices (max %u)", response->device_count, response->max_devices);

    HOST_COMM_UNLOCK(comm);
    return ESP_OK;
}

#ifdef CONFIG_PRODUCT_BLUESCSI
esp_err_t host_comm_get_initiator_status(host_comm_t *comm, initiator_status_response_t *response,
                                         size_t max_size, size_t *out_size) {
    if (!host_comm_have_handle(comm) || !response ||
        max_size < sizeof(initiator_status_response_t)) {
        return ESP_ERR_INVALID_ARG;
    }

    HOST_COMM_LOCK(comm);

    ESP_LOGD(TAG, "Getting initiator status");

    esp_err_t ret = transport_two_phase_transaction(&comm->transport,
                                                    PANEL_CMD_GET_INITIATOR_STATUS, PANEL_ARG_IGNORED,
                                                    NULL, 0,
                                                    NULL, 0);
    if (ret != ESP_OK) {
        HOST_COMM_UNLOCK(comm);
        return ret;
    }

    uint8_t *result_data;
    size_t result_size;
    ret = host_comm_poll_async_result(comm, 2000, 10, max_size, &result_data, &result_size);
    if (ret != ESP_OK) {
        HOST_COMM_UNLOCK(comm);
        return ret;
    }

    size_t copy_size = (result_size < max_size) ? result_size : max_size;
    memcpy(response, result_data, copy_size);
    if (out_size) *out_size = copy_size;
    ESP_LOGD(TAG, "Initiator status: phase=%u, targets_found=%u",
             response->phase, response->targets_found);

    HOST_COMM_UNLOCK(comm);
    return ESP_OK;
}
#endif // CONFIG_PRODUCT_BLUESCSI

esp_err_t host_comm_get_command_status(host_comm_t *comm, panel_command_status_t *status) {
    if (!host_comm_have_handle(comm) || !status) {
        return ESP_ERR_INVALID_ARG;
    }

    HOST_COMM_LOCK(comm);

    esp_err_t ret = transport_two_phase_transaction(&comm->transport,
                                           PANEL_CMD_GET_COMMAND_STATUS, PANEL_ARG_IGNORED,
                                           NULL, 0,
                                           (uint8_t*)status, sizeof(panel_command_status_t));

    HOST_COMM_UNLOCK(comm);
    return ret;
}

esp_err_t host_comm_reset(host_comm_t *comm) {
    if (!host_comm_have_handle(comm)) {
        return ESP_ERR_INVALID_STATE;
    }

    HOST_COMM_LOCK(comm);

    ESP_LOGI(TAG, "Resetting host async state");

    esp_err_t ret = transport_two_phase_transaction(&comm->transport,
                                                    PANEL_CMD_RESET, PANEL_ARG_IGNORED,
                                                    NULL, 0,
                                                    NULL, 0);
    if (ret != ESP_OK) {
        ESP_LOGE(TAG, "Failed to send reset command: %s", esp_err_to_name(ret));
    }

    HOST_COMM_UNLOCK(comm);
    return ret;
}
