polpo/open-retro-storage-frontpanel/sw-frontpanel/main/json_stream.cpp

// SPDX-License-Identifier: GPL-2.0-only
//
//  Copyright (C) 2025  Ian Scott
//
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
#include "json_stream.h"
#include <string.h>
#include <stdio.h>

JsonStreamWriter::JsonStreamWriter(httpd_req_t* req)
    : req_(req), first_item_(true), depth_(0), in_object_(false), buf_len_(0) {
}

esp_err_t JsonStreamWriter::flush() {
    if (buf_len_ == 0) return ESP_OK;
    size_t len = buf_len_;
    buf_len_ = 0;
    return httpd_resp_send_chunk(req_, buf_, len);
}

esp_err_t JsonStreamWriter::sendChunk(const char* chunk) {
    size_t len = strlen(chunk);
    if (len >= kBufSize) {
        esp_err_t ret = flush();
        if (ret != ESP_OK) return ret;
        return httpd_resp_send_chunk(req_, chunk, len);
    }
    if (buf_len_ + len > kBufSize) {
        esp_err_t ret = flush();
        if (ret != ESP_OK) return ret;
    }
    memcpy(buf_ + buf_len_, chunk, len);
    buf_len_ += len;
    return ESP_OK;
}

esp_err_t JsonStreamWriter::sendEscapedString(const char* str) {
    esp_err_t ret = sendChunk("\"");
    if (ret != ESP_OK) return ret;

    while (*str) {
        if (*str == '"' || *str == '\\') {
            char escaped[3] = {'\\', *str, '\0'};
            ret = sendChunk(escaped);
        } else if (*str == '\n') {
            ret = sendChunk("\\n");
        } else if (*str == '\r') {
            ret = sendChunk("\\r");
        } else if (*str == '\t') {
            ret = sendChunk("\\t");
        } else if ((unsigned char)*str < 0x20) {
            // JSON forbids any other raw control character in a string
            static const char hex[] = "0123456789abcdef";
            char escaped[7] = {'\\', 'u', '0', '0', hex[*str >> 4], hex[*str & 0xF], '\0'};
            ret = sendChunk(escaped);
        } else {
            char single[2] = {*str, '\0'};
            ret = sendChunk(single);
        }
        if (ret != ESP_OK) return ret;
        str++;
    }

    return sendChunk("\"");
}

esp_err_t JsonStreamWriter::writeSeparator() {
    if (!first_item_) {
        return sendChunk(",");
    }
    first_item_ = false;
    return ESP_OK;
}

esp_err_t JsonStreamWriter::beginObject() {
    esp_err_t ret = writeSeparator();
    if (ret != ESP_OK) return ret;

    ret = sendChunk("{");
    if (ret != ESP_OK) return ret;

    depth_++;
    in_object_ = true;
    first_item_ = true;
    return ESP_OK;
}

esp_err_t JsonStreamWriter::endObject() {
    esp_err_t ret = sendChunk("}");
    if (ret != ESP_OK) return ret;

    depth_--;
    first_item_ = false;
    in_object_ = (depth_ > 0);
    return ESP_OK;
}

esp_err_t JsonStreamWriter::beginArray() {
    esp_err_t ret = writeSeparator();
    if (ret != ESP_OK) return ret;

    ret = sendChunk("[");
    if (ret != ESP_OK) return ret;

    depth_++;
    in_object_ = false;
    first_item_ = true;
    return ESP_OK;
}

esp_err_t JsonStreamWriter::endArray() {
    esp_err_t ret = sendChunk("]");
    if (ret != ESP_OK) return ret;

    depth_--;
    first_item_ = false;
    return ESP_OK;
}

esp_err_t JsonStreamWriter::writeKey(const char* key) {
    esp_err_t ret = writeSeparator();
    if (ret != ESP_OK) return ret;

    ret = sendEscapedString(key);
    if (ret != ESP_OK) return ret;

    ret = sendChunk(":");
    if (ret != ESP_OK) return ret;

    // After writing a key, the next item (value) should not have a separator
    first_item_ = true;
    return ESP_OK;
}

esp_err_t JsonStreamWriter::writeString(const char* value) {
    esp_err_t ret = writeSeparator();
    if (ret != ESP_OK) return ret;

    return sendEscapedString(value);
}

esp_err_t JsonStreamWriter::writeNumber(uint32_t value) {
    esp_err_t ret = writeSeparator();
    if (ret != ESP_OK) return ret;

    char buffer[16];
    snprintf(buffer, sizeof(buffer), "%lu", value);
    return sendChunk(buffer);
}

esp_err_t JsonStreamWriter::writeNumber(int value) {
    esp_err_t ret = writeSeparator();
    if (ret != ESP_OK) return ret;

    char buffer[16];
    snprintf(buffer, sizeof(buffer), "%d", value);
    return sendChunk(buffer);
}

esp_err_t JsonStreamWriter::writeBool(bool value) {
    esp_err_t ret = writeSeparator();
    if (ret != ESP_OK) return ret;

    return sendChunk(value ? "true" : "false");
}

esp_err_t JsonStreamWriter::write(const char* key, const char* value) {
    esp_err_t ret = writeKey(key);
    if (ret != ESP_OK) return ret;

    first_item_ = true; // Reset for the value
    if (value == nullptr) {
        esp_err_t null_ret = writeSeparator();
        if (null_ret != ESP_OK) return null_ret;
        return sendChunk("null");
    }
    return writeString(value);
}

esp_err_t JsonStreamWriter::write(const char* key, uint32_t value) {
    esp_err_t ret = writeKey(key);
    if (ret != ESP_OK) return ret;

    first_item_ = true; // Reset for the value
    return writeNumber(value);
}

esp_err_t JsonStreamWriter::write(const char* key, int value) {
    esp_err_t ret = writeKey(key);
    if (ret != ESP_OK) return ret;

    first_item_ = true; // Reset for the value
    return writeNumber(value);
}

esp_err_t JsonStreamWriter::write(const char* key, bool value) {
    esp_err_t ret = writeKey(key);
    if (ret != ESP_OK) return ret;

    first_item_ = true; // Reset for the value
    return writeBool(value);
}

esp_err_t JsonStreamWriter::finalize() {
    esp_err_t ret = flush();
    if (ret != ESP_OK) return ret;
    return httpd_resp_send_chunk(req_, NULL, 0);
}
