polpo/open-retro-storage-frontpanel/sw-frontpanel/main/transport.h

// SPDX-License-Identifier: GPL-2.0-only
//
//  Copyright (C) 2025  Ian Scott
//
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
#ifndef TRANSPORT_H
#define TRANSPORT_H

#include <stdint.h>
#include <stdbool.h>
#include "esp_err.h"
#include "driver/gpio.h"
#include "transport_config.h"

// Forward declaration
typedef struct transport_handle transport_handle_t;

// Physical link to the host main board. SPI = 0 so a zeroed config selects
// SPI (the host-native tests rely on this).
typedef enum {
    TRANSPORT_TYPE_SPI = 0,
    TRANSPORT_TYPE_I2C = 1,
} transport_type_t;

// Transport operations structure
typedef struct {
    esp_err_t (*init)(transport_handle_t *handle);
    esp_err_t (*deinit)(transport_handle_t *handle);
    esp_err_t (*two_phase_transaction)(transport_handle_t *handle, 
               uint8_t command, uint16_t argument,
               const uint8_t *write_data, size_t write_len,
               uint8_t *read_data, size_t read_len);
    esp_err_t (*poll_async_status)(transport_handle_t *handle,
                                   bool *ready, uint16_t *response_size,
                                   uint8_t *result_data, size_t max_result_size);
    const char* (*get_name)(void);
} transport_ops_t;

// Transport configuration
typedef struct {
    transport_type_t type; // Which transport implementation to use
    uint8_t device_addr;  // I2C address or SPI device ID
    gpio_num_t sda_miso;  // I2C SDA or SPI MISO
    gpio_num_t scl_clk;   // I2C SCL or SPI CLK
    gpio_num_t cs;        // SPI CS (ignored for I2C)
    gpio_num_t mosi;      // SPI MOSI (ignored for I2C)
    uint32_t clock_speed; // Clock speed in Hz
    uint32_t timeout_ms;  // Operation timeout
} transport_config_t;

// Transport handle structure
struct transport_handle {
    const transport_ops_t *ops;
    transport_config_t config;
    void *priv;  // Private data for specific transport implementation
    bool initialized;
};

// Public API functions
esp_err_t transport_init(transport_handle_t *handle, const transport_config_t *config);
esp_err_t transport_deinit(transport_handle_t *handle);
esp_err_t transport_two_phase_transaction(transport_handle_t *handle,
                                          uint8_t command, uint16_t argument,
                                          const uint8_t *write_data, size_t write_len,
                                          uint8_t *read_data, size_t read_len);
esp_err_t transport_poll_async_status(transport_handle_t *handle,
                                      bool *ready, uint16_t *response_size,
                                      uint8_t *result_data, size_t max_result_size);
const char* transport_get_name(transport_handle_t *handle);

// Factory function to get the appropriate transport implementation
const transport_ops_t* transport_get_ops(transport_type_t type);

#endif // TRANSPORT_H
