polpo/open-retro-storage-frontpanel/sw-frontpanel/main/toaster_sprite.h

// SPDX-License-Identifier: GPL-2.0-only
//
//  Copyright (C) 2025  Ian Scott
//
//  Toaster sprite ported from PicoPOST (TheRealZago / fireTwoOneNine).
//  Toast sprite added locally.
//  All sprites are 24x24, MSB-first bit order (use u8g2_DrawBitmap).

#ifndef TOASTER_SPRITE_H
#define TOASTER_SPRITE_H

#include <stdint.h>

#define TOASTER_WIDTH       24
#define TOASTER_HEIGHT      24
#define TOASTER_BYTES_PER_ROW 3
#define TOASTER_FRAMES      3
#define TOASTER_FRAME_MS    100

static const uint8_t toast_frame[TOASTER_HEIGHT * TOASTER_BYTES_PER_ROW] = {
    0x00, 0x00, 0x00,
    0x00, 0x00, 0x00,
    0x00, 0x00, 0x00,
    0x00, 0x3C, 0x00,
    0x00, 0xFF, 0x00,
    0x03, 0xDF, 0x80,
    0x0E, 0xF7, 0xE0,
    0x7F, 0x85, 0xF8,
    0xF4, 0x13, 0x7C,
    0xFE, 0x81, 0xFE,
    0xEA, 0x13, 0xAF,
    0x7F, 0xC5, 0xFF,
    0x1D, 0xFF, 0x78,
    0xA7, 0xBB, 0xE2,
    0x53, 0xEF, 0x95,
    0xA8, 0xFE, 0x2A,
    0x15, 0x11, 0x54,
    0x0A, 0xAA, 0xA0,
    0x05, 0x55, 0x40,
    0x00, 0xAA, 0x00,
    0x00, 0x10, 0x00,
    0x00, 0x00, 0x00,
    0x00, 0x00, 0x00,
    0x00, 0x00, 0x00,
};

// DVD logo for the bouncing-logo screensaver style. 48x21, MSB-first.
#define DVD_LOGO_WIDTH         48
#define DVD_LOGO_HEIGHT        21
#define DVD_LOGO_BYTES_PER_ROW 6

static const uint8_t dvd_logo[DVD_LOGO_HEIGHT * DVD_LOGO_BYTES_PER_ROW] = {
    0x00, 0xF7, 0xFF, 0x01, 0xFF, 0xF0,
    0x01, 0xE7, 0xFF, 0xC3, 0xFF, 0xE0,
    0x01, 0xE7, 0xFF, 0xE3, 0xFF, 0xE0,
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
        0x77, 0xEF, 0xC8,
        0xAC, 0xF1, 0x88,
        0x2C, 0xEE, 0x18,
        0x28, 0xDD, 0x90,
        0x84, 0x7B, 0x60,
        0x44, 0x7E, 0xF8,
        0x24, 0x3F, 0xF0,
        0x1F, 0xCF, 0xF0,
        0x00, 0x03, 0xC0,
        0x00, 0x00, 0x00,
    },
};

#endif
