polpo/open-retro-storage-frontpanel/sw-frontpanel/main/ui_screens.c

// SPDX-License-Identifier: GPL-2.0-only
//
//  Copyright (C) 2025  Ian Scott
//
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
#include "ui_screens.h"
#include "fw_version.h"
#include "sdkconfig.h"
#include "esp_log.h"
#include "freertos/FreeRTOS.h"
#include "freertos/task.h"
#include <string.h>

static const char *TAG = "ui_screens";

// Horizontal text scrolling state
typedef struct {
    int16_t offset;              // Current scroll offset in pixels
    uint32_t last_update_ms;     // Last time scroll was updated
    uint32_t pause_start_ms;     // When current pause started
    bool is_paused;              // Currently paused?
    bool pause_at_end;           // Paused at end or beginning?
    bool needs_scroll;           // Does text actually need scrolling?
} text_scroll_state_t;

#define TEXT_SCROLL_SPEED_PX_PER_SEC 25
#define TEXT_SCROLL_INITIAL_PAUSE_MS 2000
#define TEXT_SCROLL_END_PAUSE_MS 1000
#define TEXT_SCROLL_UPDATE_INTERVAL_MS 50  // 20 FPS for smooth scrolling

// Helper function to update text scroll state and return current offset
static int16_t update_text_scroll_offset(text_scroll_state_t *state, uint16_t text_width, uint16_t display_width) {
    if (!state || !state->needs_scroll) {
        return 0;
    }

    uint32_t current_ms = xTaskGetTickCount() * portTICK_PERIOD_MS;

    // Handle initial pause at beginning
    if (state->is_paused && !state->pause_at_end) {
        if (current_ms - state->pause_start_ms >= TEXT_SCROLL_INITIAL_PAUSE_MS) {
            state->is_paused = false;
            state->last_update_ms = current_ms;
        }
        return 0;
    }

    // Handle pause at end
    if (state->is_paused && state->pause_at_end) {
        if (current_ms - state->pause_start_ms >= TEXT_SCROLL_END_PAUSE_MS) {
            // Reset to beginning
            state->offset = 0;
            state->is_paused = true;
            state->pause_at_end = false;
            state->pause_start_ms = current_ms;
        }
        return state->offset;
    }

    // Update scroll offset
    uint32_t elapsed_ms = current_ms - state->last_update_ms;
    if (elapsed_ms >= TEXT_SCROLL_UPDATE_INTERVAL_MS) {
        int16_t pixels_to_move = (TEXT_SCROLL_SPEED_PX_PER_SEC * elapsed_ms) / 1000;
        state->offset += pixels_to_move;
        state->last_update_ms = current_ms;

        // Check if we've scrolled past the end
        int16_t max_offset = text_width - display_width + 10; // +10 for some padding
        if (state->offset >= max_offset) {
            state->offset = max_offset;
            state->is_paused = true;
            state->pause_at_end = true;
            state->pause_start_ms = current_ms;
        }
    }

    return state->offset;
}

// Helper function to initialize/reset text scroll state
static void init_text_scroll_state(text_scroll_state_t *state, display_manager_t *display,
                                   const char *text, uint16_t available_width) {
    if (!state || !display || !text) {
        return;
    }

    // Measure text width
    uint16_t text_width = u8g2_GetStrWidth(&display->u8g2, text);

    // Determine if scrolling is needed
    state->needs_scroll = (text_width > available_width);
    state->offset = 0;
    state->last_update_ms = xTaskGetTickCount() * portTICK_PERIOD_MS;
    state->pause_start_ms = state->last_update_ms;
    state->is_paused = true;
    state->pause_at_end = false;
}

// Helper function to draw scrolling text with clipping
// Returns true if scrolling is active and needs continuous updates
static bool draw_text_scrolling(display_manager_t *display, uint8_t x, uint8_t y,
                                const char *text, uint16_t width, text_scroll_state_t *state) {
    if (!display || !text || !state) {
        return false;
    }

    if (!state->needs_scroll) {
        // No scrolling needed, draw normally
        display_manager_draw_text(display, x, y, text);
        return false;
    }

    // Get current scroll offset
    uint16_t text_width = u8g2_GetStrWidth(&display->u8g2, text);
    int16_t offset = update_text_scroll_offset(state, text_width, width);

    // Calculate text position (use signed int to handle negative positions)
    int16_t text_x = (int16_t)x - offset;

    // Set clipping region
    u8g2_SetClipWindow(&display->u8g2, x, 0, x + width, 64);

    // Draw text with offset (u8g2 handles negative coordinates)
    u8g2_DrawStr(&display->u8g2, text_x, y, text);

    // Reset clipping
    u8g2_SetMaxClipWindow(&display->u8g2);

    // Return true to indicate scrolling is active
    return true;
}

// Logo bitmaps - conditionally compiled based on product
#ifdef CONFIG_PRODUCT_BLUESCSI
// BlueSCSI text logo (128x24)
#define LOGO_WIDTH 128
#define LOGO_HEIGHT 24
static const uint8_t product_logo[] = {
  0x00, 0x00, 0x00, 0x00, 0x00, 0x00, 0x00, 0x00, 0x00, 0x00, 0x00, 0x00,
  0x00, 0x00, 0x00, 0x00, 0x00, 0x00, 0x00, 0x00, 0x00, 0x00, 0x00, 0x00,
  0x00, 0x00, 0x00, 0x00, 0x00, 0x00, 0x00, 0x00, 0x00, 0x00, 0x00, 0x00,
  0x00, 0x00, 0x00, 0x00, 0x00, 0x00, 0x00, 0x00, 0x00, 0x00, 0x00, 0x00,
  0x00, 0x00, 0x00, 0x00, 0x00, 0x00, 0x00, 0x00, 0x00, 0x00, 0x00, 0x00,
  0x00, 0x00, 0x00, 0x00, 0x00, 0x00, 0x00, 0xC0, 0x01, 0x00, 0x00, 0x00,
  0x00, 0x00, 0x00, 0x00, 0x00, 0x00, 0x00, 0x00, 0x00, 0x80, 0xFF, 0xC0,
  0x01, 0x00, 0x00, 0x00, 0xF8, 0x03, 0xF8, 0x01, 0x7F, 0xE0, 0x00, 0x00,
  0x00, 0x80, 0xFF, 0xC3, 0x01, 0x00, 0x00, 0x00, 0xFE, 0x07, 0xFE, 0x87,
  0xFF, 0xE0, 0x00, 0x00, 0x00, 0x80, 0xFF, 0xC3, 0x01, 0x00, 0x00, 0x00,
  0xFE, 0x07, 0xFF, 0xC7, 0xFF, 0xE0, 0x00, 0x00, 0x00, 0x80, 0xC7, 0xC3,
  0xE1, 0xF0, 0xE0, 0x07, 0x0F, 0x80, 0x0F, 0xC4, 0x01, 0xE0, 0x00, 0x00,
  0x00, 0x80, 0xC7, 0xC3, 0xE1, 0xF0, 0xF0, 0x0F, 0x0F, 0x80, 0x07, 0xC0,
  0x01, 0xE0, 0x00, 0x00, 0x00, 0x80, 0xFF, 0xC3, 0xE1, 0xF0, 0x78, 0x1E,
  0x3E, 0xC0, 0x03, 0xC0, 0x0F, 0xE0, 0x00, 0x00, 0x00, 0x80, 0xFF, 0xC1,
  0xE1, 0xF0, 0x38, 0x3C, 0xFE, 0xC3, 0x03, 0x80, 0x7F, 0xE0, 0x00, 0x00,
  0x00, 0x80, 0xFF, 0xC3, 0xE1, 0xF0, 0xFC, 0x3F, 0xF8, 0xC7, 0x03, 0x00,
  0xFF, 0xE1, 0x00, 0x00, 0x00, 0x80, 0x87, 0xC7, 0xE1, 0xF0, 0xFC, 0x3F,
  0x80, 0xCF, 0x03, 0x00, 0xF0, 0xE1, 0x00, 0x00, 0x00, 0x80, 0x87, 0xC7,
  0xE1, 0xF0, 0x3C, 0x00, 0x00, 0x8F, 0x07, 0x00, 0xC0, 0xE1, 0x00, 0x00,
  0x00, 0x80, 0x87, 0xC7, 0xE1, 0xF0, 0x38, 0x00, 0x02, 0x8F, 0x0F, 0x44,
  0xE0, 0xE1, 0x00, 0x00, 0x00, 0x80, 0xFF, 0xC7, 0xE1, 0xFF, 0xF8, 0x1C,
  0xFF, 0x07, 0xFF, 0xC7, 0xFF, 0xE1, 0x00, 0x00, 0x00, 0x80, 0xFF, 0xC3,
  0xE1, 0xFF, 0xF0, 0x1F, 0xFF, 0x07, 0xFE, 0xC7, 0xFF, 0xE0, 0x00, 0x00,
  0x00, 0x80, 0xFF, 0xC0, 0xC1, 0xF7, 0xE0, 0x0F, 0xFC, 0x01, 0xF8, 0x01,
  0x7F, 0xE0, 0x00, 0x00, 0x00, 0x00, 0x00, 0x00, 0x00, 0x00, 0x00, 0x00,
  0x00, 0x00, 0x00, 0x00, 0x00, 0x00, 0x00, 0x00, 0x00, 0x00, 0x00, 0x00,
  0x00, 0x00, 0x00, 0x00, 0x00, 0x00, 0x00, 0x00, 0x00, 0x00, 0x00, 0x00,
  0x00, 0x00, 0x00, 0x00, 0x00, 0x00, 0x00, 0x00, 0x00, 0x00, 0x00, 0x00,
  0x00, 0x00, 0x00, 0x00, 0x00, 0x00, 0x00, 0x00, 0x00, 0x00, 0x00, 0x00,
  0x00, 0x00, 0x00, 0x00, 0x00, 0x00, 0x00, 0x00, 0x00, 0x00, 0x00, 0x00,
  0x00, 0x00, 0x00, 0x00, 0x00, 0x00, 0x00, 0x00, 0x00, 0x00, 0x00, 0x00
};
#else
// PicoIDE logo (128x15)
#define LOGO_WIDTH 128
#define LOGO_HEIGHT 15
static const uint8_t product_logo[] = {
  0xF0, 0xFF, 0x0F, 0x7E, 0x00, 0x00, 0x00, 0x00, 0x00, 0x00, 0x3F, 0xFC,
  0xFF, 0x80, 0xFF, 0xFF, 0xF0, 0xFF, 0x1F, 0x7E, 0x00, 0x00, 0x00, 0x00,
  0x00, 0x80, 0x3F, 0xFE, 0xFF, 0xC3, 0xFF, 0x7F, 0xF0, 0x83, 0x1F, 0x00,
  0x00, 0x00, 0x00, 0x00, 0x00, 0x80, 0x1F, 0x7E, 0xF8, 0xC3, 0x0F, 0x00,
  0xF8, 0x81, 0x1F, 0x00, 0x00, 0x00, 0x00, 0x00, 0x00, 0x80, 0x1F, 0x7E,
  0xF0, 0xC7, 0x0F, 0x00, 0xF8, 0xC1, 0x1F, 0x3F, 0xFC, 0xFF, 0x87, 0xFF,
  0xFF, 0x81, 0x1F, 0x7F, 0xF0, 0xE7, 0x0F, 0x00, 0xF8, 0xC1, 0x8F, 0x3F,
  0xFE, 0xFF, 0xC3, 0xFF, 0xFF, 0xC3, 0x1F, 0x3F, 0xF0, 0xE3, 0x07, 0x00,
  0xFC, 0xC1, 0x8F, 0x1F, 0x7F, 0x00, 0xE0, 0x07, 0xF0, 0xC7, 0x0F, 0x3F,
  0xF0, 0xF3, 0x0F, 0x00, 0xFC, 0xF1, 0x87, 0x1F, 0x3F, 0x00, 0xF0, 0x07,
  0xF0, 0xC7, 0x0F, 0x3F, 0xF0, 0xFB, 0xFF, 0x00, 0xFC, 0xFE, 0x83, 0x1F,
  0x3F, 0x00, 0xF0, 0x03, 0xF0, 0xC7, 0x8F, 0x3F, 0xF8, 0xF3, 0x7F, 0x00,
  0xFC, 0x00, 0xC0, 0x9F, 0x1F, 0x00, 0xF0, 0x03, 0xF0, 0xE3, 0x87, 0x1F,
  0xF8, 0xF1, 0x03, 0x00, 0xFE, 0x00, 0xC0, 0x8F, 0x1F, 0x00, 0xF8, 0x03,
  0xF0, 0xE3, 0x87, 0x1F, 0xF8, 0xF1, 0x03, 0x00, 0x7E, 0x00, 0xC0, 0x8F,
  0x1F, 0x00, 0xF8, 0x03, 0xF0, 0xE3, 0x87, 0x1F, 0xFC, 0xF1, 0x03, 0x00,
  0x7E, 0x00, 0xC0, 0x8F, 0x3F, 0x00, 0xF0, 0x07, 0xF8, 0xF1, 0xC7, 0x1F,
  0xFE, 0xF8, 0x03, 0x00, 0x7F, 0x00, 0xE0, 0x07, 0xFF, 0xFF, 0xF0, 0xFF,
  0xFF, 0xF0, 0xC3, 0xFF, 0x7F, 0xF8, 0xFF, 0x0F, 0x3F, 0x00, 0xE0, 0x07,
  0xFE, 0xFF, 0xC0, 0xFF, 0x7F, 0xF0, 0xC3, 0xFF, 0x3F, 0xF8, 0xFF, 0x0F
};
#endif



esp_err_t ui_show_splash_screen(display_manager_t *display) {
    if (!display) {
        return ESP_ERR_INVALID_ARG;
    }

    display_manager_clear(display);
    display_manager_draw_bitmap(display, 0, 0, LOGO_WIDTH, LOGO_HEIGHT, product_logo);

    display_manager_draw_frame(display, 20, 40, 88, 8);

    display_manager_request_update(display);

    ESP_LOGI(TAG, "Splash screen initialized");
    return ESP_OK;
}

esp_err_t ui_update_splash_progress(display_manager_t *display, const char *step_text, uint8_t progress) {
    if (!display) {
        return ESP_ERR_INVALID_ARG;
    }

    display_manager_set_draw_color(display, 0);
    display_manager_draw_box(display, 20, 50, 128, 12);

    display_manager_set_draw_color(display, 1);
    display_manager_set_font(display, u8g2_font_6x10_tf);
    display_manager_draw_text(display, 22, 60, step_text ? step_text : "");

    uint8_t fill_width = (progress * 84) / 100;
    display_manager_draw_box(display, 22, 42, fill_width, 4);

    display_manager_request_update(display);

    return ESP_OK;
}

esp_err_t ui_update_splash_version(display_manager_t *display, const char *version) {
    if (!display || !version) {
        return ESP_ERR_INVALID_ARG;
    }

    // Clear the version text area
    display_manager_set_draw_color(display, 0);
    display_manager_draw_box(display, 0, 18, 128, 20);
    display_manager_set_draw_color(display, 1);

    display_manager_set_font(display, u8g2_font_6x10_tf);

    char version_text[32];
    snprintf(version_text, sizeof(version_text), "FW v%s", version);

    // Center horizontally from the rendered width so a longer "-preN"
    // prerelease suffix stays centered instead of running off the edge
    uint16_t text_width = u8g2_GetStrWidth(&display->u8g2, version_text);
    uint8_t x = text_width < 128 ? (128 - text_width) / 2 : 0;
    display_manager_draw_text(display, x, 32, version_text);

    display_manager_request_update(display);

    return ESP_OK;
}

// Draw a vertical scroll bar down the right edge from y to the bottom of the
// screen. total must be greater than visible.
static void draw_scrollbar(display_manager_t *display, uint8_t y,
                           uint32_t visible, uint32_t total, uint32_t position) {
    uint8_t scrollbar_x = 125;
    uint8_t scrollbar_width = 3;
    uint8_t scrollbar_height = 64 - y;

    // Draw scroll bar background (thin frame)
    display_manager_draw_frame(display, scrollbar_x, y, scrollbar_width, scrollbar_height);

    // Calculate thumb position and size
    uint8_t thumb_height = (visible * (scrollbar_height - 2)) / total;
    if (thumb_height < 4) thumb_height = 4; // Minimum thumb size

    uint8_t max_thumb_pos = scrollbar_height - 2 - thumb_height;
    uint8_t thumb_y = y + 1 + (position * max_thumb_pos) / (total - visible);

    // Draw scroll thumb (filled box)
    display_manager_draw_box(display, scrollbar_x + 1, thumb_y, scrollbar_width - 2, thumb_height);
}

esp_err_t ui_draw_menu(display_manager_t *display, menu_t *menu) {
    if (!display || !menu) {
        return ESP_ERR_INVALID_ARG;
    }

    // Clear display
    display_manager_clear(display);

    // Draw header if title provided
    uint8_t y_offset = 0;
    if (menu->title) {
        display_manager_set_font(display, u8g2_font_6x10_tf);
        display_manager_draw_box(display, 0, 0, 128, 10);
        display_manager_set_draw_color(display, 0);
        display_manager_draw_text(display, 2, 8, menu->title);
        display_manager_set_draw_color(display, 1);
        y_offset = 10;
    }

    // Get visible menu items
    menu_item_t *visible_items;
    uint32_t visible_count;
    uint32_t cursor_pos;

    esp_err_t ret = menu_get_visible_items(menu, &visible_items, &visible_count, &cursor_pos);
    if (ret != ESP_OK) {
        return ret;
    }

    // Set font for menu items
    display_manager_set_font(display, u8g2_font_amstrad_cpc_extended_8f);

    // Allocate text scroll state if not already allocated
    if (!menu->text_scroll_state) {
        menu->text_scroll_state = calloc(1, sizeof(text_scroll_state_t));
    }

    text_scroll_state_t *scroll_state = (text_scroll_state_t *)menu->text_scroll_state;
    uint8_t highlight_width = (menu->item_count > menu->visible_items) ? 122 : 128;

    // Initialize scroll state for selected item (animation function will use this)
    if (scroll_state && cursor_pos < visible_count) {
        init_text_scroll_state(scroll_state, display, visible_items[cursor_pos].text, highlight_width - 4);
    }

    // Draw each visible menu item
    for (uint32_t i = 0; i < visible_count; i++) {
        uint8_t y_pos = y_offset + (i + 1) * 8;

        // Highlight selected item
        if (i == cursor_pos) {
            display_manager_draw_box(display, 0, y_pos - 8, highlight_width, 8);
            display_manager_set_draw_color(display, 0); // Inverted text
            display_manager_draw_text(display, 2, y_pos, visible_items[i].text);
            display_manager_set_draw_color(display, 1);
        } else {
            // Draw non-selected items normally
            display_manager_draw_text(display, 2, y_pos, visible_items[i].text);
        }
    }

    // Draw scroll bar if there are more items than visible
    if (menu->item_count > menu->visible_items) {
        draw_scrollbar(display, y_offset, menu->visible_items, menu->item_count, menu->window_start);
    }

    // Request display update
    display_manager_request_update(display);

    // Clear redraw flag - full draw is complete
    // Animation will be triggered separately via ui_menu_needs_animation()
    menu_clear_redraw_flag(menu);

    return ESP_OK;
}

// Check if menu has active scrolling animation
bool ui_menu_needs_animation(menu_t *menu) {
    if (!menu) {
        return false;
    }
    text_scroll_state_t *scroll_state = (text_scroll_state_t *)menu->text_scroll_state;
    return scroll_state && scroll_state->needs_scroll;
}

// Lightweight menu animation - only updates the selected item's scrolling text
// Returns true if animation is active and display was updated
bool ui_animate_menu(display_manager_t *display, menu_t *menu) {
    if (!display || !menu) {
        return false;
    }

    text_scroll_state_t *scroll_state = (text_scroll_state_t *)menu->text_scroll_state;
    if (!scroll_state || !scroll_state->needs_scroll) {
        return false;
    }

    // Get cursor position and visible items info
    menu_item_t *visible_items;
    uint32_t visible_count;
    uint32_t cursor_pos;

    esp_err_t ret = menu_get_visible_items(menu, &visible_items, &visible_count, &cursor_pos);
    if (ret != ESP_OK || cursor_pos >= visible_count) {
        return false;
    }

    // Calculate y position
    uint8_t y_offset = menu->title ? 10 : 0;
    uint8_t y_pos = y_offset + (cursor_pos + 1) * 8;
    uint8_t highlight_width = (menu->item_count > menu->visible_items) ? 122 : 128;

    // Set font and colors
    display_manager_set_font(display, u8g2_font_amstrad_cpc_extended_8f);

    // Clear and redraw just the selected item row
    display_manager_set_draw_color(display, 1);
    display_manager_draw_box(display, 0, y_pos - 8, highlight_width, 8);
    display_manager_set_draw_color(display, 0);

    // Draw scrolling text
    draw_text_scrolling(display, 2, y_pos, visible_items[cursor_pos].text, highlight_width - 4, scroll_state);

    display_manager_set_draw_color(display, 1);
    display_manager_request_update(display);

    return true;
}

esp_err_t ui_draw_disc_list(display_manager_t *display, menu_t *menu) {
    // Use the regular menu drawing - menu->title should be set appropriately
    return ui_draw_menu(display, menu);
}

esp_err_t ui_draw_status_bar(display_manager_t *display, const char *status) {
    if (!display || !status) {
        return ESP_ERR_INVALID_ARG;
    }
    
    // Draw status bar at bottom of screen
    display_manager_set_font(display, u8g2_font_6x10_tf);
    display_manager_draw_box(display, 0, 56, 128, 8);
    display_manager_set_draw_color(display, 0);
    display_manager_draw_text(display, 2, 63, status);
    display_manager_set_draw_color(display, 1);
    
    display_manager_request_update(display);
    
    return ESP_OK;
}

#define INFO_LINE_CHARS    20  // ~20 chars fit between x=2 and the scroll bar
#define INFO_VISIBLE_LINES 5   // baselines at y=20,30,40,50,60

// Copy the next wrapped line of info text into line (INFO_LINE_CHARS + 1 bytes)
// and return a pointer to the start of the following line
static const char *info_next_line(const char *p, char *line) {
    int len = 0;
    while (*p && *p != '\n' && len < INFO_LINE_CHARS) {
        line[len++] = *p++;
    }
    line[len] = '\0';
    if (*p == '\n') p++;
    return p;
}

uint32_t ui_info_screen_max_scroll(const char *info) {
    if (!info) {
        return 0;
    }

    char line[INFO_LINE_CHARS + 1];
    uint32_t count = 0;
    while (*info) {
        info = info_next_line(info, line);
        count++;
    }
    return (count > INFO_VISIBLE_LINES) ? count - INFO_VISIBLE_LINES : 0;
}

esp_err_t ui_draw_info_screen(display_manager_t *display, const char *title,
                              const char *info, uint32_t first_line) {
    if (!display || !title || !info) {
        return ESP_ERR_INVALID_ARG;
    }

    display_manager_clear(display);

    // Draw title
    display_manager_set_font(display, u8g2_font_amstrad_cpc_extended_8f);
    display_manager_draw_box(display, 0, 0, 128, 10);
    display_manager_set_draw_color(display, 0);
    display_manager_draw_text(display, 2, 8, title);
    display_manager_set_draw_color(display, 1);

    display_manager_set_font(display, u8g2_font_6x10_tf);

    // Draw info text, hard wrapped at INFO_LINE_CHARS, starting at first_line
    uint32_t max_scroll = ui_info_screen_max_scroll(info);
    if (first_line > max_scroll) first_line = max_scroll;

    int y = 20;
    int line_height = 10;
    char line[INFO_LINE_CHARS + 1];
    const char *p = info;

    for (uint32_t i = 0; i < first_line && *p; i++) {
        p = info_next_line(p, line);
    }

    while (*p && y < 64) {
        p = info_next_line(p, line);
        display_manager_draw_text(display, 2, y, line);
        y += line_height;
    }

    // Draw scroll bar if the text doesn't fit (same style as menus)
    if (max_scroll > 0) {
        draw_scrollbar(display, 10, INFO_VISIBLE_LINES, max_scroll + INFO_VISIBLE_LINES, first_line);
    }

    display_manager_request_update(display);

    return ESP_OK;
}

esp_err_t ui_draw_firmware_update(display_manager_t *display, const char *status, uint8_t progress) {
    if (!display || !status) {
        return ESP_ERR_INVALID_ARG;
    }

    display_manager_clear(display);

    // Draw title
    display_manager_set_font(display, u8g2_font_amstrad_cpc_extended_8f);
    display_manager_draw_text(display, 10, 12, "Firmware Update");

    // Draw status text
    display_manager_set_font(display, u8g2_font_6x10_tr);
    display_manager_draw_text(display, 5, 28, status);

    // Draw progress bar frame
    display_manager_draw_frame(display, 10, 40, 108, 12);

    // Draw progress bar fill
    if (progress > 0) {
        uint8_t fill_width = (progress * 104) / 100;
        display_manager_set_draw_color(display, 1);
        display_manager_draw_box(display, 12, 42, fill_width, 8);
    }

    // Draw progress percentage
    char progress_text[16];
    snprintf(progress_text, sizeof(progress_text), "%d%%", progress);
    display_manager_draw_text(display, 54, 62, progress_text);

    display_manager_request_update(display);

    // FW updates count as activity — keep the display awake so dim/screensaver
    // don't engage over the progress UI.
    display_manager_wake(display);

    return ESP_OK;
}

#ifdef CONFIG_PRODUCT_BLUESCSI
esp_err_t ui_draw_firmware_status(display_manager_t *display,
                                  uint32_t panel_current_ver, uint32_t panel_avail_ver, bool panel_update_avail,
                                  uint32_t main_current_ver, uint32_t main_avail_ver, bool main_update_avail,
                                  uint8_t selection) {
#else
esp_err_t ui_draw_firmware_status(display_manager_t *display,
                                  uint32_t current_ver, uint32_t avail_ver,
                                  bool update_avail) {
#endif
    if (!display) {
        return ESP_ERR_INVALID_ARG;
    }

    display_manager_clear(display);

    // Title bar
    display_manager_set_font(display, u8g2_font_6x10_tf);
    display_manager_draw_box(display, 0, 0, 128, 12);
    display_manager_set_draw_color(display, 0);
    display_manager_draw_text(display, 2, 10, "Firmware Update");
    display_manager_set_draw_color(display, 1);

    char version_str[20];

#ifdef CONFIG_PRODUCT_BLUESCSI
    int y = 24;
    const int row_height = 12;

    // Panel firmware row
    if (selection == 0) {
        display_manager_draw_box(display, 0, y - 9, 128, row_height);
        display_manager_set_draw_color(display, 0);
    }
    display_manager_draw_text(display, 2, y, "Panel:");
    fw_version_format_panel(version_str, sizeof(version_str), panel_current_ver);
    display_manager_draw_text(display, 44, y, version_str);
    if (panel_update_avail) {
        display_manager_draw_text(display, 79, y, "->");
        fw_version_format_panel(version_str, sizeof(version_str), panel_avail_ver);
        display_manager_draw_text(display, 94, y, version_str);
    }
    if (selection == 0) {
        display_manager_set_draw_color(display, 1);
    }
    
    y += row_height;

    // Main board firmware row
    if (selection == 1) {
        display_manager_draw_box(display, 0, y - 9, 128, row_height);
        display_manager_set_draw_color(display, 0);
    }
    display_manager_draw_text(display, 2, y, "Main:");
    fw_version_format_mainboard(version_str, sizeof(version_str), main_current_ver);
    display_manager_draw_text(display, 44, y, version_str);
    if (main_update_avail) {
        display_manager_draw_text(display, 79, y, "->");
        fw_version_format_mainboard(version_str, sizeof(version_str), main_avail_ver);
        display_manager_draw_text(display, 94, y, version_str);
    }
    if (selection == 1) {
        display_manager_set_draw_color(display, 1);
    }

    // Instructions at bottom
    bool has_update = (selection == 0 && panel_update_avail) ||
                      (selection == 1 && main_update_avail);

    if (has_update) {
        display_manager_draw_text(display, 0, 62, "[>] Update  [<] Back");
    } else {
        display_manager_draw_text(display, 0, 62, "No updates  [<] Back");
    }
#else
    // System version (main board version is user-facing)
    display_manager_draw_text(display, 2, 26, "Version:");
    fw_version_format_mainboard(version_str, sizeof(version_str), current_ver);
    display_manager_draw_text(display, 56, 26, version_str);

    // Available version
    if (update_avail) {
        display_manager_draw_text(display, 2, 40, "Available:");
        fw_version_format_mainboard(version_str, sizeof(version_str), avail_ver);
        display_manager_draw_text(display, 68, 40, version_str);
    } else {
        display_manager_draw_text(display, 2, 40, "Up to date");
    }

    // Instructions at bottom
    if (update_avail) {
        display_manager_draw_text(display, 0, 62, "[>] Update  [<] Back");
    } else {
        display_manager_draw_text(display, 0, 62, "[<] Back");
    }
#endif

    display_manager_request_update(display);

    return ESP_OK;
}

// Helper to extract directory name from path (returns pointer into path)
// Examples: "/cdrom" -> "cdrom", "/foo/bar" -> "bar", "/" -> "/", "cdrom" -> "cdrom"
static const char* get_directory_name(const char *path) {
    if (!path || !path[0]) {
        return "/";
    }

    size_t len = strlen(path);

    // Skip trailing slashes
    while (len > 1 && path[len - 1] == '/') {
        len--;
    }

    // Find last slash before the end
    const char *end = path + len;
    const char *last_slash = NULL;
    for (const char *p = path; p < end; p++) {
        if (*p == '/') {
            last_slash = p;
        }
    }

    // If no slash, or only a leading slash with content after, return after the slash
    if (!last_slash) {
        return path;  // No slash at all, e.g., "cdrom"
    }
    if (last_slash == path && len > 1) {
        return path + 1;  // Leading slash only, e.g., "/cdrom" -> "cdrom"
    }
    if (last_slash == path && len == 1) {
        return "/";  // Root directory
    }
    return last_slash + 1;  // e.g., "/foo/bar" -> "bar"
}

// Module-level state for status screen animation
static text_scroll_state_t status_title_scroll_state = {0};
static char status_title_text[64] = "";
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
